robert-lippmann/ft-RPI-sa/Software/include/S32K142/S32K142_features.h

/*
 * Copyright (c) 2015 Freescale Semiconductor, Inc.
 * Copyright 2016-2023 NXP
 *
 * NXP Confidential and Proprietary. This software is owned or controlled by NXP
 * and may only be used strictly in accordance with the applicable license terms.
 * By expressly accepting such terms or by downloading, installing, activating
 * and/or otherwise using the software, you are agreeing that you have read, and
 * that you agree to comply with and are bound by, such license terms. If you do
 * not agree to be bound by the applicable license terms, then you may not retain,
 * install, activate or otherwise use the software.
 */

/*!
 * @file S32K142_features.h
 * @brief Chip specific module features
 *
 * @page misra_violations MISRA-C:2012 violations
 *
 * @section [global]
 * Violates MISRA 2012 Advisory Rule 2.3, Global typedef not referenced.
 * Type used only in some modules of the SDK.
 *
 * @section [global]
 * Violates MISRA 2012 Advisory Rule 2.4, tag unused outside of typedefs
 * Tag defined specifically for typedef
 *
 * @section [global]
 * Violates MISRA 2012 Advisory Rule 2.5, Global macro not referenced.
 * The macros defined are used to define features for each driver, so this might be reported
 * when the analysis is made only on one driver.
 *
 * @section [global]
 * Violates MISRA 2012 Advisory Directive 4.9, Function-like macro
 * These are very simple macros used for abstracting hw implementation.
 * They help make the code easy to understand.
 *
 * @section [global]
 * Violates MISRA 2012 Required Rule 5.1, identifier clash
 * The supported compilers use more than 31 significant characters for identifiers.
 *
 * @section [global]
 * Violates MISRA 2012 Required Rule 5.2, identifier clash
 * The supported compilers use more than 31 significant characters for identifiers.
 *
 * @section [global]
 * Violates MISRA 2012 Required Rule 5.4, identifier clash
 * The supported compilers use more than 31 significant characters for identifiers.
 *
 * @section [global]
 * Violates MISRA 2012 Required Rule 5.5, identifier clash
 * The supported compilers use more than 31 significant characters for identifiers.
 *
 */

#if !defined(S32K142_FEATURES_H)
#define S32K142_FEATURES_H

/* ERRATA sections*/

/* @brief ARM Errata 838869: Store immediate overlapping exception return operation might vector to
 * incorrect interrupt. */
#define ERRATA_E9005

/* @brief ARM Errata 709718: VDIV or VSQRT instructions might not complete correctly when very
 * short ISRs are used. */
#define ERRATA_E6940

/* @brief E10792: LPI2C: Slave Transmit Data Flag may incorrectly read as one when TXCFG is zero.
 * Interrupts for transfer data should be enabled after the address valid event is detected and
 * disabled at the end of the transfer. */
#define ERRATA_E10792

/* @brief Errata workaround: System clock status register may be a erroneous status during the system clock switch.
 * Read system clock source twice. */
#define ERRATA_E10777

/* @brief E10856: FTM: Safe state is not removed from channel outputs after fault condition
 * ends if SWOCTRL is being used to control the pin */
#define ERRATA_E10856

/* @brief Number of cores. */
#define NUMBER_OF_CORES (1u)

/* @brief Number of alternative clocks available */
#define NUMBER_OF_ALT_CLOCKS  ADC_CLK_ALT_1

/* PORT module features */
/*! @brief PORT Used for setting Pins */
#define FEATURE_PINS_DRIVER_USING_PORT (1)
/* @brief Has control lock (register bit PCR[LK]). */
#define FEATURE_PORT_HAS_PIN_CONTROL_LOCK (1)
/* @brief Has open drain control (register bit PCR[ODE]). */
#define FEATURE_PINS_HAS_OPEN_DRAIN (0)
/* @brief Has digital filter (registers DFER, DFCR and DFWR). */
#define FEATURE_PORT_HAS_DIGITAL_FILTER (1)
/* @brief Has trigger output to trigger other peripherals (register bit field PCR[IRQC] values). */
#define FEATURE_PORT_HAS_TRIGGER_OUT (0)
/* @brief Has setting flag only (register bit field PCR[IRQC] values). */
#define FEATURE_PORT_HAS_FLAG_SET_ONLY (0)
/* @brief Has over-current feature (register bit field PCR[OCIE] values). */
#define FEATURE_PINS_HAS_OVER_CURRENT (0)
/* @brief Has pull resistor selection available. */
#define FEATURE_PINS_HAS_PULL_SELECTION (1)
/* @brief Has slew rate control (register bit PCR[SRE]). */
#define FEATURE_PINS_HAS_SLEW_RATE (0)
/* @brief Has passive filter (register bit field PCR[PFE]). */
#define FEATURE_PORT_HAS_PASSIVE_FILTER (1)
/* @brief Has drive strength (register bit PCR[DSE]). */
#define FEATURE_PINS_HAS_DRIVE_STRENGTH (1)
/* @brief Has drive strength control bits*/
#define FEATURE_PINS_HAS_DRIVE_STRENGTH_CONTROL (0)
/* @brief Has port input disable control bits*/
#define FEATURE_PORT_HAS_INPUT_DISABLE (1)
/* @brief SIM_CHIPCTL_ADC_INTERLEAVE_EN bit is available */
#define FEATURE_PINS_HAS_ADC_INTERLEAVE_EN (1)

/* CMP module features */

/* @brief Comparator hard block offset control */
#define FEATURE_CMP_HAS_HARD_BLOCK_OFFSET   (1)
/* @brief Comparator fix DAC input to mux side */
#define FEATURE_CMP_DAC_FIX_SELECTION       (0)
/* @brief Comparator initialization delay */
#define FEATURE_CMP_HAS_INIT_DELAY          (1)

#define C0_RESET_VALUE (CMP_C0_DMAEN(0U) | CMP_C0_IER(0U) | CMP_C0_IEF(0U) | CMP_C0_CFR(1U) |                     \
                        CMP_C0_CFF(1U) | CMP_C0_FPR(0U) | CMP_C0_SE(0U) | CMP_C0_WE(0U) |                         \
                        CMP_C0_PMODE(0U) | CMP_C0_INVT(0U) | CMP_C0_COS(0U) | CMP_C0_OPE(0U) |                    \
                        CMP_C0_EN(0U) | CMP_C0_FILTER_CNT(0U) | CMP_C0_OFFSET(0U) | CMP_C0_HYSTCTR(0U))

#define C1_RESET_VALUE (CMP_C1_INPSEL(0U) | CMP_C1_INNSEL(0U) | CMP_C1_CHN7(0U) | CMP_C1_CHN6(0U) |               \
                        CMP_C1_CHN5(0U) | CMP_C1_CHN4(0U) | CMP_C1_CHN3(0U) | CMP_C1_CHN2(0U) |                   \
                        CMP_C1_CHN1(0U) | CMP_C1_CHN0(0U) | CMP_C1_DACEN(0U) | CMP_C1_VRSEL(0U) |                 \
                        CMP_C1_PSEL(0U) | CMP_C1_MSEL(0U) |  CMP_C1_VOSEL(0U))

#define C2_RESET_VALUE (CMP_C2_RRE(0U) | CMP_C2_RRIE(0U) | CMP_C2_FXMP(0U) | CMP_C2_FXMXCH(0U) | CMP_C2_CH7F(1U) |    \
                        CMP_C2_CH6F(1U) | CMP_C2_CH5F(1U) | CMP_C2_CH4F(1U) | CMP_C2_CH3F(1U) | CMP_C2_CH2F(1U) |     \
                        CMP_C2_CH1F(1U) | CMP_C2_CH0F(1U) | CMP_C2_NSAM(0U) | CMP_C2_NSAM(0U) | CMP_C2_INITMOD(0U) |  \
                        CMP_C2_ACOn(0U))

#define CMP_DAC_SOURCE          0U
#define CMP_MUX_SOURCE          1U
#define CMP_DAC_RESOLUTION      255U

/* SOC module features */

/* @brief PORT availability on the SoC. */
#define FEATURE_SOC_PORT_COUNT (5)

#define FEATURE_SOC_SCG_COUNT (1)

/* @brief Slow IRC high range clock frequency. */
#define FEATURE_SCG_SIRC_HIGH_RANGE_FREQ (8000000U)

/* @brief Fast IRC trimmed clock frequency(48MHz). */
#define FEATURE_SCG_FIRC_FREQ0  (48000000U)

/* FLASH module features */

/* @brief Is of type FTFA. */
#define FEATURE_FLS_IS_FTFA (0u)
/* @brief Is of type FTFC. */
#define FEATURE_FLS_IS_FTFC (1u)
/* @brief Is of type FTFE. */
#define FEATURE_FLS_IS_FTFE (0u)
/* @brief Is of type FTFL. */
#define FEATURE_FLS_IS_FTFL (0u)
/* @brief Is of type FTFM. */
#define FEATURE_FLS_IS_FTFM (0u)
/* @brief Has flags indicating the status of the FlexRAM (register bits FCNFG[EEERDY], FCNFG[RAMRDY] and FCNFG[PFLSH]). */
#define FEATURE_FLS_HAS_FLEX_RAM_FLAGS (1u)
/* @brief Has program flash swapping status flag (register bit FCNFG[SWAP]). */
#define FEATURE_FLS_HAS_PF_SWAPPING_STATUS_FLAG (0u)
/* @brief Has EEPROM region protection (register FEPROT). */
#define FEATURE_FLS_HAS_EEROM_REGION_PROTECTION (1u)
/* @brief Has data flash region protection (register FDPROT). */
#define FEATURE_FLS_HAS_DATA_FLS_REGION_PROTECTION (1u)
/* @brief P-Flash block count. */
#define FEATURE_FLS_PF_BLOCK_COUNT (1u)
/* @brief P-Flash block size. */
#define FEATURE_FLS_PF_BLOCK_SIZE (0x40000u)
/* @brief P-Flash sector size. */
#define FEATURE_FLS_PF_BLOCK_SECTOR_SIZE (2048u)
/* @brief P-Flash write unit size. */
#define FEATURE_FLS_PF_BLOCK_WRITE_UNIT_SIZE (8u)
/* @brief P-Flash block swap feature. */
#define FEATURE_FLS_HAS_PF_BLOCK_SWAP (0u)
/* @brief Has FlexNVM memory. */
#define FEATURE_FLS_HAS_FLEX_NVM (1u)
/* @brief FlexNVM block count. */
#define FEATURE_FLS_DF_BLOCK_COUNT (1u)
/* @brief FlexNVM block size. */
#define FEATURE_FLS_DF_BLOCK_SIZE (65536u)
/* @brief FlexNVM sector size. */
#define FEATURE_FLS_DF_BLOCK_SECTOR_SIZE (2048u)
/* @brief FlexNVM write unit size. */
#define FEATURE_FLS_DF_BLOCK_WRITE_UNIT_SIZE (8u)
/* @brief FlexNVM start address. (Valid only if FlexNVM is available.) */
#define FEATURE_FLS_DF_START_ADDRESS (0x10000000u)
/* @brief Has FlexRAM memory. */
#define FEATURE_FLS_HAS_FLEX_RAM (1u)
/* @brief FlexRAM size. */
#define FEATURE_FLS_FLEX_RAM_SIZE (4096u)
/* @brief FlexRAM start address. (Valid only if FlexRAM is available.) */
#define FEATURE_FLS_FLEX_RAM_START_ADDRESS (0x14000000u)
/* @brief Has 0x00 Read 1s Block command. */
#define FEATURE_FLS_HAS_READ_1S_BLOCK_CMD (1u)
/* @brief Has 0x01 Read 1s Section command. */
#define FEATURE_FLS_HAS_READ_1S_SECTION_CMD (1u)
/* @brief Has 0x02 Program Check command. */
#define FEATURE_FLS_HAS_PROGRAM_CHECK_CMD (1u)
/* @brief Has 0x03 Read Resource command. */
#define FEATURE_FLS_HAS_READ_RESOURCE_CMD (0u)
/* @brief Has 0x06 Program Longword command. */
#define FEATURE_FLS_HAS_PROGRAM_LONGWORD_CMD (0u)
/* @brief Has 0x07 Program Phrase command. */
#define FEATURE_FLS_HAS_PROGRAM_PHRASE_CMD (1u)
/* @brief Has 0x08 Erase Flash Block command. */
#define FEATURE_FLS_HAS_ERASE_BLOCK_CMD (1u)
/* @brief Has 0x09 Erase Flash Sector command. */
#define FEATURE_FLS_HAS_ERASE_SECTOR_CMD (1u)
/* @brief Has 0x0B Program Section command. */
#define FEATURE_FLS_HAS_PROGRAM_SECTION_CMD (1u)
/* @brief Has 0x40 Read 1s All Blocks command. */
#define FEATURE_FLS_HAS_READ_1S_ALL_BLOCKS_CMD (1u)
/* @brief Has 0x41 Read Once command. */
#define FEATURE_FLS_HAS_READ_ONCE_CMD (1u)
/* @brief Has 0x43 Program Once command. */
#define FEATURE_FLS_HAS_PROGRAM_ONCE_CMD (1u)
/* @brief Has 0x44 Erase All Blocks command. */
#define FEATURE_FLS_HAS_ERASE_ALL_CMD (1u)
/* @brief Has 0x45 Verify Backdoor Access Key command. */
#define FEATURE_FLS_HAS_VERIFY_BACKDOOR_ACCESS_KEY_CMD (1u)
/* @brief Has 0x46 Swap Control command. */
#define FEATURE_FLS_HAS_SWAP_CONTROL_CMD (0u)
/* @brief Has 0x49 Erase All Blocks unsecure command. */
#define FEATURE_FLS_HAS_ERASE_ALL_BLOCKS_UNSECURE_CMD (1u)
/* @brief Has 0x80 Program Partition command. */
#define FEATURE_FLS_HAS_PROGRAM_PARTITION_CMD (1u)
/* @brief Has 0x81 Set FlexRAM Function command. */
#define FEATURE_FLS_HAS_SET_FLEXRAM_FUNCTION_CMD (1u)
/* @brief P-Flash Erase/Read 1st all block command address alignment. */
#define FEATURE_FLS_PF_BLOCK_CMD_ADDRESS_ALIGMENT (8u)
/* @brief P-Flash Erase sector command address alignment. */
#define FEATURE_FLS_PF_SECTOR_CMD_ADDRESS_ALIGMENT (8u)
/* @brief P-Flash Program/Verify section command address alignment. */
#define FEATURE_FLS_PF_SECTION_CMD_ADDRESS_ALIGMENT (8u)
/* @brief P-Flash Read resource command address alignment. */
#define FEATURE_FLS_PF_RESOURCE_CMD_ADDRESS_ALIGMENT (8u)
/* @brief P-Flash Program check command address alignment. */
#define FEATURE_FLS_PF_CHECK_CMD_ADDRESS_ALIGMENT (4u)
/* @brief P-Flash Program check command address alignment. */
#define FEATURE_FLS_PF_SWAP_CONTROL_CMD_ADDRESS_ALIGMENT (0u)
/* @brief FlexNVM Erase/Read 1st all block command address alignment. */
#define FEATURE_FLS_DF_BLOCK_CMD_ADDRESS_ALIGMENT (8u)
/* @brief FlexNVM Erase sector command address alignment. */
#define FEATURE_FLS_DF_SECTOR_CMD_ADDRESS_ALIGMENT (8u)
/* @brief FlexNVM Program/Verify section command address alignment. */
#define FEATURE_FLS_DF_SECTION_CMD_ADDRESS_ALIGMENT (8u)
/* @brief FlexNVM Read resource command address alignment. */
#define FEATURE_FLS_DF_RESOURCE_CMD_ADDRESS_ALIGMENT (8u)
/* @brief FlexNVM Program check command address alignment. */
#define FEATURE_FLS_DF_CHECK_CMD_ADDRESS_ALIGMENT (4u)
/* @brief FlexNVM partition code 0000 mapping to data flash size in bytes (0xFFFFFFFF = reserved). */
#define FEATURE_FLS_DF_SIZE_0000 (0x00010000u)
/* @brief FlexNVM partition code 0001 mapping to data flash size in bytes (0xFFFFFFFF = reserved). */
#define FEATURE_FLS_DF_SIZE_0001 (0xFFFFFFFFu)
/* @brief FlexNVM partition code 0010 mapping to data flash size in bytes (0xFFFFFFFF = reserved). */
#define FEATURE_FLS_DF_SIZE_0010 (0xFFFFFFFFu)
/* @brief FlexNVM partition code 0011 mapping to data flash size in bytes (0xFFFFFFFF = reserved). */
#define FEATURE_FLS_DF_SIZE_0011 (0x00008000u)
/* @brief FlexNVM partition code 0100 mapping to data flash size in bytes (0xFFFFFFFF = reserved). */
#define FEATURE_FLS_DF_SIZE_0100 (0x00000000u)
/* @brief FlexNVM partition code 0101 mapping to data flash size in bytes (0xFFFFFFFF = reserved). */
#define FEATURE_FLS_DF_SIZE_0101 (0xFFFFFFFFu)
/* @brief FlexNVM partition code 0110 mapping to data flash size in bytes (0xFFFFFFFF = reserved). */
#define FEATURE_FLS_DF_SIZE_0110 (0xFFFFFFFFu)
/* @brief FlexNVM partition code 0111 mapping to data flash size in bytes (0xFFFFFFFF = reserved). */
#define FEATURE_FLS_DF_SIZE_0111 (0xFFFFFFFFu)
/* @brief FlexNVM partition code 1000 mapping to data flash size in bytes (0xFFFFFFFF = reserved). */
#define FEATURE_FLS_DF_SIZE_1000 (0x00000000u)
/* @brief FlexNVM partition code 1001 mapping to data flash size in bytes (0xFFFFFFFF = reserved). */
#define FEATURE_FLS_DF_SIZE_1001 (0xFFFFFFFFu)
/* @brief FlexNVM partition code 1010 mapping to data flash size in bytes (0xFFFFFFFF = reserved). */
#define FEATURE_FLS_DF_SIZE_1010 (0x00004000u)
/* @brief FlexNVM partition code 1011 mapping to data flash size in bytes (0xFFFFFFFF = reserved). */
#define FEATURE_FLS_DF_SIZE_1011 (0x00008000u)
/* @brief FlexNVM partition code 1100 mapping to data flash size in bytes (0xFFFFFFFF = reserved). */
#define FEATURE_FLS_DF_SIZE_1100 (0x00010000u)
/* @brief FlexNVM partition code 1101 mapping to data flash size in bytes (0xFFFFFFFF = reserved). */
#define FEATURE_FLS_DF_SIZE_1101 (0xFFFFFFFFu)
/* @brief FlexNVM partition code 1110 mapping to data flash size in bytes (0xFFFFFFFF = reserved). */
#define FEATURE_FLS_DF_SIZE_1110 (0xFFFFFFFFu)
/* @brief FlexNVM partition code 1111 mapping to data flash size in bytes (0xFFFFFFFF = reserved). */
#define FEATURE_FLS_DF_SIZE_1111 (0x00010000u)
/* @brief Emulated EEPROM size code 0000 mapping to emulated EEPROM size in bytes (0xFFFF = reserved). */
#define FEATURE_FLS_EE_SIZE_0000 (0xFFFFu)
/* @brief Emulated EEPROM size code 0001 mapping to emulated EEPROM size in bytes (0xFFFF = reserved). */
#define FEATURE_FLS_EE_SIZE_0001 (0xFFFFu)
/* @brief Emulated EEPROM size code 0010 mapping to emulated EEPROM size in bytes (0xFFFF = reserved). */
#define FEATURE_FLS_EE_SIZE_0010 (0x1000u)
/* @brief Emulated EEPROM size code 0011 mapping to emulated EEPROM size in bytes (0xFFFF = reserved). */
#define FEATURE_FLS_EE_SIZE_0011 (0xFFFFu)
/* @brief Emulated EEPROM size code 0100 mapping to emulated EEPROM size in bytes (0xFFFF = reserved). */
#define FEATURE_FLS_EE_SIZE_0100 (0xFFFFu)
/* @brief Emulated EEPROM size code 0101 mapping to emulated EEPROM size in bytes (0xFFFF = reserved). */
#define FEATURE_FLS_EE_SIZE_0101 (0xFFFFu)
/* @brief Emulated EEPROM size code 0110 mapping to emulated EEPROM size in bytes (0xFFFF = reserved). */
#define FEATURE_FLS_EE_SIZE_0110 (0xFFFFu)
/* @brief Emulated EEPROM size code 0111 mapping to emulated EEPROM size in bytes (0xFFFF = reserved). */
#define FEATURE_FLS_EE_SIZE_0111 (0xFFFFu)
/* @brief Emulated EEPROM size code 1000 mapping to emulated EEPROM size in bytes (0xFFFF = reserved). */
#define FEATURE_FLS_EE_SIZE_1000 (0xFFFFu)
/* @brief Emulated EEPROM size code 1001 mapping to emulated EEPROM size in bytes (0xFFFF = reserved). */
#define FEATURE_FLS_EE_SIZE_1001 (0xFFFFu)
/* @brief Emulated EEPROM size code 1010 mapping to emulated EEPROM size in bytes (0xFFFF = reserved). */
#define FEATURE_FLS_EE_SIZE_1010 (0xFFFFu)
/* @brief Emulated EEPROM size code 1011 mapping to emulated EEPROM size in bytes (0xFFFF = reserved). */
#define FEATURE_FLS_EE_SIZE_1011 (0xFFFFu)
/* @brief Emulated EEPROM size code 1100 mapping to emulated EEPROM size in bytes (0xFFFF = reserved). */
#define FEATURE_FLS_EE_SIZE_1100 (0xFFFFu)
/* @brief Emulated EEPROM size code 1101 mapping to emulated EEPROM size in bytes (0xFFFF = reserved). */
#define FEATURE_FLS_EE_SIZE_1101 (0xFFFFu)
/* @brief Emulated EEPROM size code 1110 mapping to emulated EEPROM size in bytes (0xFFFF = reserved). */
#define FEATURE_FLS_EE_SIZE_1110 (0xFFFFu)
/* @brief Emulated EEPROM size code 1111 mapping to emulated EEPROM size in bytes (0xFFFF = reserved). */
#define FEATURE_FLS_EE_SIZE_1111 (0x0000u)
/* @brief Has the detection of uncorrected ECC errors. */
#define FEATURE_FLS_HAS_DETECT_ECC_ERROR (1)
/* @brief Has the interrupt double bit fault detect. */
#define FEATURE_FLS_HAS_INTERRUPT_DOUBLE_BIT_FAULT_IRQ (1)

/* LPUART module features */

/* @brief Has extended data register ED. */
#define FEATURE_LPUART_HAS_EXTENDED_DATA_REGISTER_FLAGS (1)
/* @brief Hardware flow control (RTS, CTS) is supported. */
#define FEATURE_LPUART_HAS_MODEM_SUPPORT (1)
/* @brief Baud rate oversampling is available. */
#define FEATURE_LPUART_HAS_BAUD_RATE_OVER_SAMPLING_SUPPORT (1)
/* @brief Baud rate oversampling is available. */
#define FEATURE_LPUART_HAS_BOTH_EDGE_SAMPLING_SUPPORT (1)
/* @brief Capacity (number of entries) of the transmit/receive FIFO (or zero if no FIFO is available). */
#define FEATURE_LPUART_FIFO_SIZE (4U)
/* @brief Supports two match addresses to filter incoming frames. */
#define FEATURE_LPUART_HAS_ADDRESS_MATCHING (1)
/* @brief Has transmitter/receiver DMA enable bits. */
#define FEATURE_LPUART_HAS_DMA_ENABLE (1)
/* @brief Flag clearance mask for STAT register. */
#define FEATURE_LPUART_STAT_REG_FLAGS_MASK (0xC01FC000U)
/* @brief Flag clearance mask for FIFO register. */
#define FEATURE_LPUART_FIFO_REG_FLAGS_MASK (0x00030000U)
/* @brief Reset mask for FIFO register. */
#define FEATURE_LPUART_FIFO_RESET_MASK (0x0003C000U)
/* @brief Default oversampling ratio. */
#define FEATURE_LPUART_DEFAULT_OSR (0x0FUL)
/* @brief Default baud rate modulo divisor. */
#define FEATURE_LPUART_DEFAULT_SBR (0x04UL)
/* @brief Clock names for LPUART. */
#define LPUART_CLOCK_NAMES {LPUART0_CLK, LPUART1_CLK}

/* FlexIO module features */

/* @brief Define the maximum number of shifters for any FlexIO instance. */
#define FEATURE_FLEXIO_MAX_SHIFTER_COUNT  (4U)
/* @brief Define DMA request names for Flexio. */
#define FEATURE_FLEXIO_DMA_REQ_0    EDMA_REQ_FLEXIO_SHIFTER0
#define FEATURE_FLEXIO_DMA_REQ_1    EDMA_REQ_FLEXIO_SHIFTER1
#define FEATURE_FLEXIO_DMA_REQ_2    EDMA_REQ_FLEXIO_SHIFTER2
#define FEATURE_FLEXIO_DMA_REQ_3    EDMA_REQ_FLEXIO_SHIFTER3

/* LPI2C module features */

/* @brief DMA instance used for LPI2C module */
#define LPI2C_DMA_INSTANCE 0U

/* @brief EDMA requests for LPI2C module. */
#define LPI2C_EDMA_REQ                           {{(uint8_t)EDMA_REQ_LPI2C0_TX, (uint8_t)EDMA_REQ_LPI2C0_RX}}
/* @brief PCC clocks for LPI2C module. */
#define LPI2C_PCC_CLOCKS                         {LPI2C0_CLK}

/* @brief Disable high-speed and ultra-fast operating modes for S32K14x. */
#define LPI2C_HAS_FAST_PLUS_MODE (0U)
#define LPI2C_HAS_HIGH_SPEED_MODE (0U)
#define LPI2C_HAS_ULTRA_FAST_MODE (0U)

/* @brief VECTKEY value so that AIRCR register write is not ignored. */
#define FEATURE_SCB_VECTKEY               (0x05FAU)


/* SMC module features */

/* @brief Has stop option (register bit STOPCTRL[STOPO]). */
#define FEATURE_SMC_HAS_STOPO (1U)
/* @brief Has partial stop option (register bit STOPCTRL[PSTOPO]). */
#define FEATURE_SMC_HAS_PSTOPO (0U)
/* @brief Has WAIT and VLPW options. */
#define FEATURE_SMC_HAS_WAIT_VLPW (0U)
/* @brief Has high speed run mode (register bit PMPROT[AHSRUN]). */
#define FEATURE_SMC_HAS_HIGH_SPEED_RUN_MODE (1U)
/* @brief Value of SPLL source clock in the SCG_HCCR register */
#define FEATURE_SCG_SPLL_VALUE (6U)

/* RCM module feature */

/* @brief Has existence of CMU loss of clock as reset source */
#define FEATURE_RCM_HAS_EXISTENCE_CMU_LOSS_OF_CLOCK (0)
/* @brief Has CMU loss of clock as reset source */
#define FEATURE_RCM_HAS_CMU_LOSS_OF_CLOCK (0)
/* @brief Has sticky CMU loss of clock as reset source */
#define FEATURE_RCM_HAS_STICKY_CMU_LOSS_OF_CLOCK (0)

/* MPU module features */


/* @brief Specifies hardware revision level. */
#define FEATURE_MPU_HARDWARE_REVISION_LEVEL   (1U)
/* @brief Has process identifier support. */
#define FEATURE_MPU_HAS_PROCESS_IDENTIFIER    (1U)
/* @brief Special region descriptor. */
#define FEATURE_MPU_SPECIAL_REGION            (0U)
/* @brief The number of master has process identifier. */
#define FEATURE_MPU_NUM_MASTER_HAS_PROCESS_IDENTIFIER    (2U)
/* Reset value of all master access right in region 0 */
#define FEATURE_MPU_REGION_0_ACCESS_RIGHT_RESET_VALUE    (0x0061F7DFU)
/* @brief Specifies total number of bus masters. */
#define FEATURE_MPU_MASTER_COUNT              (3U)
/* @brief Specifies maximum number of masters which have separated
privilege rights for user and supervisor mode accesses (e.g. master0~3 in S32K14x).
*/
#define FEATURE_MPU_MAX_LOW_MASTER_NUMBER     (3U)
/* @brief Specifies maximum number of masters which have only
read and write permissions (e.g. master4~7 in S32K14x).
*/
#define FEATURE_MPU_MAX_HIGH_MASTER_NUMBER    (7U)

/* @brief Specifies number of set access control right bits for
   masters which have separated privilege rights for user and
   supervisor mode accesses (e.g. master0~3 in S32K14x).
*/
#define FEATURE_MPU_LOW_MASTER_CONTROL_WIDTH  (6U)
/* @brief Specifies number of set access control right bits for
   masters which have only read and write permissions(e.g. master4~7 in S32K14x).
*/
#define FEATURE_MPU_HIGH_MASTER_CONTROL_WIDTH (2U)

/* @brief The MPU Logical Bus Master Number for core bus master. */
#define FEATURE_MPU_MASTER_CORE               (0U)
/* @brief The MPU Logical Bus Master Number for Debugger master. */
#define FEATURE_MPU_MASTER_DEBUGGER           (1U)
/* @brief The MPU Logical Bus Master Number for DMA master. */
#define FEATURE_MPU_MASTER_DMA                (2U)
/* @brief Specifies master number. */
#define FEATURE_MPU_MASTER                        \
{                                                 \
    FEATURE_MPU_MASTER_CORE,     /*!< CORE */     \
    FEATURE_MPU_MASTER_DEBUGGER, /*!< DEBUGGER */ \
    FEATURE_MPU_MASTER_DMA,      /*!< DMA */      \
}

/* @brief Specifies total number of slave ports. */
#define FEATURE_MPU_SLAVE_COUNT               (4U)
/* @brief The MPU Slave Port Assignment for Flash Controller and boot ROM. */
#define FEATURE_MPU_SLAVE_FLASH_BOOTROM       (0U)
/* @brief The MPU Slave Port Assignment for SRAM back door. */
#define FEATURE_MPU_SLAVE_SRAM_BACKDOOR       (1U)
/* @brief The MPU Slave Port Assignment for SRAM_L front door. */
#define FEATURE_MPU_SLAVE_SRAM_L_FRONTDOOR    (2U)
/* @brief The MPU Slave Port Assignment for SRAM_U front door. */
#define FEATURE_MPU_SLAVE_SRAM_U_FRONTDOOR    (3U)
/* @brief The MPU Slave Port mask. */
#define FEATURE_MPU_SLAVE_MASK                (0xF0000000U)
#define FEATURE_MPU_SLAVE_SHIFT               (28u)
#define FEATURE_MPU_SLAVE_WIDTH               (4u)
#define FEATURE_MPU_SLAVE(x)                  (((uint32_t)(((uint32_t)(x))<<FEATURE_MPU_SLAVE_SHIFT))&FEATURE_MPU_SLAVE_MASK)


/* WDOG module features */

/* @brief The 32-bit value used for unlocking the WDOG. */
#define FEATURE_WDOG_UNLOCK_VALUE                       (0xD928C520U)
/* @brief The 32-bit value used for resetting the WDOG counter. */
#define FEATURE_WDOG_TRIGGER_VALUE                      (0xB480A602U)
/* @brief The reset value of the timeout register. */
#define FEATURE_WDOG_TO_RESET_VALUE                     (0x400U)
/* @brief The value minimum of the timeout register. */
#define FEATURE_WDOG_MINIMUM_TIMEOUT_VALUE              (0x0U)
/* @brief The reset value of the window register. */
#define FEATURE_WDOG_WIN_RESET_VALUE                    (0x0U)
/* @brief The mask of the reserved bit in the CS register. */
#define FEATURE_WDOG_CS_RESERVED_MASK                   (0x2000U)
/* @brief The value used to set WDOG source clock from LPO. */
#define FEATURE_WDOG_CLK_FROM_LPO                       (0x1UL)
/* @brief The first 16-bit value used for unlocking the WDOG. */
#define FEATURE_WDOG_UNLOCK16_FIRST_VALUE               (0xC520U)
/* @brief The second 16-bit value used for unlocking the WDOG. */
#define FEATURE_WDOG_UNLOCK16_SECOND_VALUE              (0xD928U)
/* @brief The first 16-bit value used for resetting the WDOG counter. */
#define FEATURE_WDOG_TRIGGER16_FIRST_VALUE              (0xA602U)
/* @brief The second 16-bit value used for resetting the WDOG counter. */
#define FEATURE_WDOG_TRIGGER16_SECOND_VALUE             (0xB480U)
/* @brief Default reset value of the CS register. */
#define FEATURE_WDOG_CS_RESET_VALUE                     (0x2520U)

/* FTM module features */

/* @brief Number of PWM channels */
#define FEATURE_FTM_CHANNEL_COUNT               (8U)
/* @brief Number of fault channels */
#define FTM_FEATURE_FAULT_CHANNELS              (4U)
/* @brief Width of control channel */
#define FTM_FEATURE_COMBINE_CHAN_CTRL_WIDTH     (8U)
/* @brief Output channel offset */
#define FTM_FEATURE_OUTPUT_CHANNEL_OFFSET       (16U)
/* @brief Max counter value */
#define FTM_FEATURE_CNT_MAX_VALUE_U32           (0x0000FFFFU)
/* @brief Input capture for single shot */
#define FTM_FEATURE_INPUT_CAPTURE_SINGLE_SHOT   (2U)
/* @brief Dithering has supported on the generated PWM signals */
#define FEATURE_FTM_HAS_SUPPORTED_DITHERING     (1U)
/*! @brief Number of interrupt vector for channels of the FTM module. */
#define FEATURE_FTM_HAS_NUM_IRQS_CHANS          (4U)

/* CRC module features */

/* @brief CRC module use for S32K. */
#define FEATURE_CRC_DRIVER_SOFT_POLYNOMIAL
/* @brief Default CRC bit width */
#define FEATURE_CRC_DEFAULT_WIDTH               CRC_BITS_16
/* @brief Default CRC read transpose */
#define FEATURE_CRC_DEFAULT_READ_TRANSPOSE      CRC_TRANSPOSE_NONE
/* @brief Default CRC write transpose */
#define FEATURE_CRC_DEFAULT_WRITE_TRANSPOSE     CRC_TRANSPOSE_NONE
/* @brief Default polynomial 0x1021U */
#define FEATURE_CRC_DEFAULT_POLYNOMIAL          (0x1021U)
/* @brief Default seed value is 0xFFFFU */
#define FEATURE_CRC_DEFAULT_SEED                (0xFFFFU)

/* EWM module features */

/* @brief First byte of the EWM Service key        */
#define FEATURE_EWM_KEY_FIRST_BYTE      (0xB4U)
/* @brief Second byte of the EWM Service key       */
#define FEATURE_EWM_KEY_SECOND_BYTE     (0x2CU)
/* @brief EWM Compare High register maximum value  */
#define FEATURE_EWM_CMPH_MAX_VALUE      (0xFEU)
/* @brief EWM Compare Low register minimum value  */
#define FEATURE_EWM_CMPL_MIN_VALUE      (0x00U)

/* @brief Supports high speed run mode. */
#define FEATURE_HAS_HIGH_SPEED_RUN_MODE  (1U)
/* @brief Supports SPLL clock source. */
#define FEATURE_HAS_SPLL_CLK             (1U)
/* @brief Supports LPO peripheral clock source. */
#define FEATURE_HAS_LPO_PERIPHERAL_CLOCK_SOURCE (0U)

/*! @brief Clock names. */
typedef enum {

    /* Main clocks */
    CORE_CLK                     = 0u,       /*!< Core clock                     */
    BUS_CLK                      = 1u,       /*!< Bus clock                      */
    SLOW_CLK                     = 2u,       /*!< Slow clock                     */
    CLKOUT_CLK                   = 3u,       /*!< CLKOUT clock                   */

    /* Other internal clocks used by peripherals. */
    SIRC_CLK                     = 4u,       /*!< SIRC clock                     */
    FIRC_CLK                     = 5u,       /*!< FIRC clock                     */
    SOSC_CLK                     = 6u,       /*!< SOSC clock                     */
    SPLL_CLK                     = 7u,       /*!< SPLL clock                     */
    RTC_CLKIN_CLK                = 8u,       /*!< RTC_CLKIN clock                */
    SCG_CLKOUT_CLK               = 9u,       /*!< SCG CLK_OUT clock              */

    SIRCDIV1_CLK                 = 10u,      /*!< SIRCDIV1 functional clock      */
    SIRCDIV2_CLK                 = 11u,      /*!< SIRCDIV2 functional clock      */
    FIRCDIV1_CLK                 = 12u,      /*!< FIRCDIV1 functional clock      */
    FIRCDIV2_CLK                 = 13u,      /*!< FIRCDIV2 functional clock      */
    SOSCDIV1_CLK                 = 14u,      /*!< SOSCDIV1 functional clock      */
    SOSCDIV2_CLK                 = 15u,      /*!< SOSCDIV2 functional clock      */
    SPLLDIV1_CLK                 = 16u,      /*!< SPLLDIV1 functional clock      */
    SPLLDIV2_CLK                 = 17u,      /*!< SPLLDIV2 functional clock      */

    SCG_END_OF_CLOCKS            = 18u,      /*!< End of SCG clocks              */

    /* SIM clocks */
    SIM_FTM0_CLOCKSEL            = 21u,      /*!< FTM0 External Clock Pin Select */
    SIM_FTM1_CLOCKSEL            = 22u,      /*!< FTM1 External Clock Pin Select */
    SIM_FTM2_CLOCKSEL            = 23u,      /*!< FTM2 External Clock Pin Select */
    SIM_FTM3_CLOCKSEL            = 24u,      /*!< FTM3 External Clock Pin Select */
    SIM_CLKOUTSELL               = 25u,      /*!< CLKOUT Select                  */
    SIM_RTCCLK_CLK               = 26u,      /*!< RTCCLK clock                   */
    SIM_LPO_CLK                  = 27u,      /*!< LPO clock                      */
    SIM_LPO_1K_CLK               = 28u,      /*!< LPO 1KHz clock                 */
    SIM_LPO_32K_CLK              = 29u,      /*!< LPO 32KHz clock                */
    SIM_LPO_128K_CLK             = 30u,      /*!< LPO 128KHz clock               */
    SIM_EIM_CLK                  = 31u,      /*!< EIM clock source               */
    SIM_ERM_CLK                  = 32u,      /*!< ERM clock source               */
    SIM_DMA_CLK                  = 33u,      /*!< DMA clock source               */
    SIM_MPU_CLK                  = 34u,      /*!< MPU clock source               */
    SIM_MSCM_CLK                 = 35u,      /*!< MSCM clock source              */
    SIM_END_OF_CLOCKS            = 36u,      /*!< End of SIM clocks              */

    /* PCC clocks */
    CMP0_CLK                     = 41u,      /*!< CMP0 clock source              */
    CRC0_CLK                     = 42u,      /*!< CRC0 clock source              */
    DMAMUX0_CLK                  = 43u,      /*!< DMAMUX0 clock source           */
    EWM0_CLK                     = 44u,      /*!< EWM0 clock source              */
    PORTA_CLK                    = 45u,      /*!< PORTA clock source             */
    PORTB_CLK                    = 46u,      /*!< PORTB clock source             */
    PORTC_CLK                    = 47u,      /*!< PORTC clock source             */
    PORTD_CLK                    = 48u,      /*!< PORTD clock source             */
    PORTE_CLK                    = 49u,      /*!< PORTE clock source             */
    RTC0_CLK                     = 50u,      /*!< RTC0 clock source              */
    PCC_END_OF_BUS_CLOCKS        = 51u,      /*!< End of BUS clocks              */
    FlexCAN0_CLK                 = 52u,      /*!< FlexCAN0 clock source          */
    FlexCAN1_CLK                 = 53u,      /*!< FlexCAN1 clock source          */
    PDB0_CLK                     = 54u,      /*!< PDB0 clock source              */
    PDB1_CLK                     = 55u,      /*!< PDB1 clock source              */
    PCC_END_OF_SYS_CLOCKS        = 56u,      /*!< End of SYS clocks              */
    FTFC0_CLK                    = 57u,      /*!< FTFC0 clock source             */
    PCC_END_OF_SLOW_CLOCKS       = 58u,      /*!< End of SLOW clocks             */
    FTM0_CLK                     = 59u,      /*!< FTM0 clock source              */
    FTM1_CLK                     = 60u,      /*!< FTM1 clock source              */
    FTM2_CLK                     = 61u,      /*!< FTM2 clock source              */
    FTM3_CLK                     = 62u,      /*!< FTM3 clock source              */
    PCC_END_OF_ASYNCH_DIV1_CLOCKS= 63u,      /*!< End of ASYNCH DIV1 clocks      */
    ADC0_CLK                     = 64u,      /*!< ADC0 clock source              */
    ADC1_CLK                     = 65u,      /*!< ADC1 clock source              */
    FLEXIO0_CLK                  = 66u,      /*!< FLEXIO0 clock source           */
    LPI2C0_CLK                   = 67u,      /*!< LPI2C0 clock source            */
    LPIT0_CLK                    = 68u,      /*!< LPIT0 clock source             */
    LPSPI0_CLK                   = 69u,      /*!< LPSPI0 clock source            */
    LPSPI1_CLK                   = 70u,      /*!< LPSPI1 clock source            */
    LPTMR0_CLK                   = 71u,      /*!< LPTMR0 clock source            */
    LPUART0_CLK                  = 72u,      /*!< LPUART0 clock source           */
    LPUART1_CLK                  = 73u,      /*!< LPUART1 clock source           */
    PCC_END_OF_ASYNCH_DIV2_CLOCKS= 74u,      /*!< End of ASYNCH DIV2 clocks      */
    PCC_END_OF_CLOCKS            = 75u,      /*!< End of PCC clocks              */
    CLOCK_NAME_COUNT             = 76u,      /*!< The total number of entries    */
} clock_names_t;

#define PCC_INVALID_INDEX  0

  /*! @brief PCC clock name mappings
   *  Mappings between clock names and peripheral clock control indexes.
   *  If there is no peripheral clock control index for a clock name,
   *  then the corresponding value is PCC_INVALID_INDEX.
   */
#define PCC_CLOCK_NAME_MAPPINGS \
{                                                                                \
PCC_INVALID_INDEX,                  /*!< Core clock                      0  */   \
PCC_INVALID_INDEX,                  /*!< Bus clock                       1  */   \
PCC_INVALID_INDEX,                  /*!< Slow clock                      2  */   \
PCC_INVALID_INDEX,                  /*!< CLKOUT clock                    3  */   \
PCC_INVALID_INDEX,                  /*!< SIRC clock                      4  */   \
PCC_INVALID_INDEX,                  /*!< FIRC clock                      5  */   \
PCC_INVALID_INDEX,                  /*!< SOSC clock                      6  */   \
PCC_INVALID_INDEX,                  /*!< SPLL clock                      7  */   \
PCC_INVALID_INDEX,                  /*!< RTC_CLKIN clock                 8  */   \
PCC_INVALID_INDEX,                  /*!< SCG CLK_OUT clock               9  */   \
PCC_INVALID_INDEX,                  /*!< SIRCDIV1 functional clock       10 */   \
PCC_INVALID_INDEX,                  /*!< SIRCDIV2 functional clock       11 */   \
PCC_INVALID_INDEX,                  /*!< FIRCDIV1 functional clock       12 */   \
PCC_INVALID_INDEX,                  /*!< FIRCDIV2 functional clock       13 */   \
PCC_INVALID_INDEX,                  /*!< SOSCDIV1 functional clock       14 */   \
PCC_INVALID_INDEX,                  /*!< SOSCDIV2 functional clock       15 */   \
PCC_INVALID_INDEX,                  /*!< SPLLDIV1 functional clock       16 */   \
PCC_INVALID_INDEX,                  /*!< SPLLDIV2 functional clock       17 */   \
PCC_INVALID_INDEX,                  /*!< End of SCG clocks               18 */   \
PCC_INVALID_INDEX,                  /*!< No clock entry in clock_names_t 19 */   \
PCC_INVALID_INDEX,                  /*!< No clock entry in clock_names_t 20 */   \
PCC_INVALID_INDEX,                  /*!< FTM0 External Clock Pin Select  21 */   \
PCC_INVALID_INDEX,                  /*!< FTM1 External Clock Pin Select  22 */   \
PCC_INVALID_INDEX,                  /*!< FTM2 External Clock Pin Select  23 */   \
PCC_INVALID_INDEX,                  /*!< FTM3 External Clock Pin Select  24 */   \
PCC_INVALID_INDEX,                  /*!< CLKOUT Select                   25 */   \
PCC_INVALID_INDEX,                  /*!< CLK32K clock                    26 */   \
PCC_INVALID_INDEX,                  /*!< LPO clock                       27 */   \
PCC_INVALID_INDEX,                  /*!< LPO 1KHz clock                  28 */   \
PCC_INVALID_INDEX,                  /*!< LPO 32KHz clock                 29 */   \
PCC_INVALID_INDEX,                  /*!< LPO 128KHz clock                30 */   \
PCC_INVALID_INDEX,                  /*!< EIM clock source                31 */   \
PCC_INVALID_INDEX,                  /*!< ERM clock source                32 */   \
PCC_INVALID_INDEX,                  /*!< DMA clock source                33 */   \
PCC_INVALID_INDEX,                  /*!< MPU clock source                34 */   \
PCC_INVALID_INDEX,                  /*!< MSCM clock source               35 */   \
PCC_INVALID_INDEX,                  /*!< No clock entry in clock_names_t 36 */   \
PCC_INVALID_INDEX,                  /*!< No clock entry in clock_names_t 37 */   \
PCC_INVALID_INDEX,                  /*!< No clock entry in clock_names_t 38 */   \
PCC_INVALID_INDEX,                  /*!< No clock entry in clock_names_t 39 */   \
PCC_INVALID_INDEX,                  /*!< No clock entry in clock_names_t 40 */   \
PCC_CMP0_INDEX,                     /*!< CMP0 clock source               41 */   \
PCC_CRC_INDEX,                      /*!< CRC clock source                42 */   \
PCC_DMAMUX_INDEX,                   /*!< DMAMUX clock source             43 */   \
PCC_EWM_INDEX,                      /*!< EWM clock source                44 */   \
PCC_PORTA_INDEX,                    /*!< PORTA clock source              45 */   \
PCC_PORTB_INDEX,                    /*!< PORTB clock source              46 */   \
PCC_PORTC_INDEX,                    /*!< PORTC clock source              47 */   \
PCC_PORTD_INDEX,                    /*!< PORTD clock source              48 */   \
PCC_PORTE_INDEX,                    /*!< PORTE clock source              49 */   \
PCC_RTC_INDEX,                      /*!< RTC clock source                50 */   \
PCC_INVALID_INDEX,                  /*!< End of BUS clocks               51 */   \
PCC_FlexCAN0_INDEX,                 /*!< FlexCAN0 clock source           52 */   \
PCC_FlexCAN1_INDEX,                 /*!< FlexCAN1 clock source           53 */   \
PCC_PDB0_INDEX,                     /*!< PDB0 clock source               54 */   \
PCC_PDB1_INDEX,                     /*!< PDB1 clock source               55 */   \
PCC_INVALID_INDEX,                  /*!< End of SYS clocks               56 */   \
PCC_FTFC_INDEX,                     /*!< FTFC clock source               57 */   \
PCC_INVALID_INDEX,                  /*!< End of SLOW clocks              58 */   \
PCC_FTM0_INDEX,                     /*!< FTM0 clock source               59 */   \
PCC_FTM1_INDEX,                     /*!< FTM1 clock source               60 */   \
PCC_FTM2_INDEX,                     /*!< FTM2 clock source               61 */   \
PCC_FTM3_INDEX,                     /*!< FTM3 clock source               62 */   \
PCC_INVALID_INDEX,                  /*!< End of ASYNCH DIV1 clocks       63 */   \
PCC_ADC0_INDEX,                     /*!< ADC0 clock source               64 */   \
PCC_ADC1_INDEX,                     /*!< ADC1 clock source               65 */   \
PCC_FlexIO_INDEX,                   /*!< FLEXIO clock source             66 */   \
PCC_LPI2C0_INDEX,                   /*!< LPI2C0 clock source             67 */   \
PCC_LPIT_INDEX,                     /*!< LPIT clock source               68 */   \
PCC_LPSPI0_INDEX,                   /*!< LPSPI0 clock source             69 */   \
PCC_LPSPI1_INDEX,                   /*!< LPSPI1 clock source             70 */   \
PCC_LPTMR0_INDEX,                   /*!< LPTMR0 clock source             71 */   \
PCC_LPUART0_INDEX,                  /*!< LPUART0 clock source            72 */   \
PCC_LPUART1_INDEX,                  /*!< LPUART1 clock source            73 */   \
PCC_INVALID_INDEX,                  /*!< End of ASYNCH DIV2 clocks       74 */   \
PCC_INVALID_INDEX,                  /*!< End of PCC clocks               75 */   \
}

/*! @brief Peripheral instance features
 *  List of features that are supported by a peripheral instance
 */
#define NO_PERIPHERAL_FEATURE                   (0U)         /* It's not a peripheral instance, there is no peripheral feature. */
#define HAS_CLOCK_GATING_IN_SIM                 (1U << 0U)   /* Clock gating is implemented in SIM (it's not in PCC) */
#define HAS_MULTIPLIER                          (1U << 1U)   /* Multiplier is implemented in PCC */
#define HAS_DIVIDER                             (1U << 2U)   /* Divider is implemented in PCC */
#define HAS_PROTOCOL_CLOCK_FROM_ASYNC1          (1U << 3U)   /* Functional clock source is provided by the first asynchronous clock. */
#define HAS_PROTOCOL_CLOCK_FROM_ASYNC2          (1U << 4U)   /* Functional clock source is provided by the second asynchronous clock. */
#define HAS_INT_CLOCK_FROM_BUS_CLOCK            (1U << 5U)   /* Interface clock is provided by the bus clock. */
#define HAS_INT_CLOCK_FROM_SYS_CLOCK            (1U << 6U)   /* Interface clock is provided by the sys clock. */
#define HAS_INT_CLOCK_FROM_SLOW_CLOCK           (1U << 7U)   /* Interface clock is provided by the slow clock. */

/*! @brief Peripheral features.
*  List of features for each clock name. If a clock name is not
*  a peripheral, no feature is supported.
*/
#define PERIPHERAL_FEATURES \
{                                                                                                                                                \
(NO_PERIPHERAL_FEATURE),                                                                            /*!< Core clock                      0  */   \
(NO_PERIPHERAL_FEATURE),                                                                            /*!< Bus clock                       1  */   \
(NO_PERIPHERAL_FEATURE),                                                                            /*!< Slow clock                      2  */   \
(NO_PERIPHERAL_FEATURE),                                                                            /*!< CLKOUT clock                    3  */   \
(NO_PERIPHERAL_FEATURE),                                                                            /*!< SIRC clock                      4  */   \
(NO_PERIPHERAL_FEATURE),                                                                            /*!< FIRC clock                      5  */   \
(NO_PERIPHERAL_FEATURE),                                                                            /*!< SOSC clock                      6  */   \
(NO_PERIPHERAL_FEATURE),                                                                            /*!< SPLL clock                      7  */   \
(NO_PERIPHERAL_FEATURE),                                                                            /*!< RTC_CLKIN clock                 8  */   \
(NO_PERIPHERAL_FEATURE),                                                                            /*!< SCG CLK_OUT clock               9  */   \
(NO_PERIPHERAL_FEATURE),                                                                            /*!< End of SCG clocks               10 */   \
(NO_PERIPHERAL_FEATURE),                                                                            /*!< No clock entry in clock_names_t 11 */   \
(NO_PERIPHERAL_FEATURE),                                                                            /*!< No clock entry in clock_names_t 12 */   \
(NO_PERIPHERAL_FEATURE),                                                                            /*!< No clock entry in clock_names_t 13 */   \
(NO_PERIPHERAL_FEATURE),                                                                            /*!< No clock entry in clock_names_t 14 */   \
(NO_PERIPHERAL_FEATURE),                                                                            /*!< No clock entry in clock_names_t 15 */   \
(NO_PERIPHERAL_FEATURE),                                                                            /*!< No clock entry in clock_names_t 16 */   \
(NO_PERIPHERAL_FEATURE),                                                                            /*!< No clock entry in clock_names_t 17 */   \
(NO_PERIPHERAL_FEATURE),                                                                            /*!< No clock entry in clock_names_t 18 */   \
(NO_PERIPHERAL_FEATURE),                                                                            /*!< No clock entry in clock_names_t 19 */   \
(NO_PERIPHERAL_FEATURE),                                                                            /*!< No clock entry in clock_names_t 20 */   \
(NO_PERIPHERAL_FEATURE),                                                                            /*!< FTM0 External Clock Pin Select  21 */   \
(NO_PERIPHERAL_FEATURE),                                                                            /*!< FTM1 External Clock Pin Select  22 */   \
(NO_PERIPHERAL_FEATURE),                                                                            /*!< FTM2 External Clock Pin Select  23 */   \
(NO_PERIPHERAL_FEATURE),                                                                            /*!< FTM3 External Clock Pin Select  24 */   \
(NO_PERIPHERAL_FEATURE),                                                                            /*!< CLKOUT Select                   25 */   \
(NO_PERIPHERAL_FEATURE),                                                                            /*!< CLK32K clock                    26 */   \
(NO_PERIPHERAL_FEATURE),                                                                            /*!< LPO clock                       27 */   \
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
(NO_PERIPHERAL_FEATURE),                                                                            /*!< End of SYS clocks               56 */   \
(HAS_INT_CLOCK_FROM_SLOW_CLOCK),                                                                    /*!< FTFC clock source               57 */   \
(NO_PERIPHERAL_FEATURE),                                                                            /*!< End of SLOW clocks              58 */   \
(HAS_PROTOCOL_CLOCK_FROM_ASYNC1 | HAS_INT_CLOCK_FROM_SYS_CLOCK),                                    /*!< FTM0 clock source               59 */   \
(HAS_PROTOCOL_CLOCK_FROM_ASYNC1 | HAS_INT_CLOCK_FROM_SYS_CLOCK),                                    /*!< FTM1 clock source               60 */   \
(HAS_PROTOCOL_CLOCK_FROM_ASYNC1 | HAS_INT_CLOCK_FROM_SYS_CLOCK),                                    /*!< FTM2 clock source               61 */   \
(HAS_PROTOCOL_CLOCK_FROM_ASYNC1 | HAS_INT_CLOCK_FROM_SYS_CLOCK),                                    /*!< FTM3 clock source               62 */   \
(NO_PERIPHERAL_FEATURE),                                                                            /*!< End of ASYNCH DIV1 clocks       63 */   \
(HAS_PROTOCOL_CLOCK_FROM_ASYNC2 | HAS_INT_CLOCK_FROM_BUS_CLOCK),                                    /*!< ADC0 clock source               64 */   \
(HAS_PROTOCOL_CLOCK_FROM_ASYNC2 | HAS_INT_CLOCK_FROM_BUS_CLOCK),                                    /*!< ADC1 clock source               65 */   \
(HAS_PROTOCOL_CLOCK_FROM_ASYNC2 | HAS_INT_CLOCK_FROM_BUS_CLOCK),                                    /*!< FLEXIO clock source             66 */   \
(HAS_PROTOCOL_CLOCK_FROM_ASYNC2 | HAS_INT_CLOCK_FROM_BUS_CLOCK),                                    /*!< LPI2C0 clock source             67 */   \
(HAS_PROTOCOL_CLOCK_FROM_ASYNC2 | HAS_INT_CLOCK_FROM_BUS_CLOCK),                                    /*!< LPIT clock source               68 */   \
(HAS_PROTOCOL_CLOCK_FROM_ASYNC2 | HAS_INT_CLOCK_FROM_BUS_CLOCK),                                    /*!< LPSPI0 clock source             69 */   \
(HAS_PROTOCOL_CLOCK_FROM_ASYNC2 | HAS_INT_CLOCK_FROM_BUS_CLOCK),                                    /*!< LPSPI1 clock source             70 */   \
(HAS_MULTIPLIER | HAS_DIVIDER | HAS_PROTOCOL_CLOCK_FROM_ASYNC2 | HAS_INT_CLOCK_FROM_BUS_CLOCK),     /*!< LPTMR0 clock source             71 */   \
(HAS_PROTOCOL_CLOCK_FROM_ASYNC2 | HAS_INT_CLOCK_FROM_BUS_CLOCK),                                    /*!< LPUART0 clock source            72 */   \
(HAS_PROTOCOL_CLOCK_FROM_ASYNC2 | HAS_INT_CLOCK_FROM_BUS_CLOCK),                                    /*!< LPUART1 clock source            73 */   \
(NO_PERIPHERAL_FEATURE),                                                                            /*!< End of ASYNCH DIV2 clocks       74 */   \
(NO_PERIPHERAL_FEATURE),                                                                            /*!< End of PCC clocks               75 */   \
}


/* Time to wait for SIRC to stabilize (number of
 * cycles when core runs at maximum speed - 112 MHz */
#define SIRC_STABILIZATION_TIMEOUT 100U

/* Time to wait for FIRC to stabilize (number of
 * cycles when core runs at maximum speed - 112 MHz */
#define FIRC_STABILIZATION_TIMEOUT 100U

/* Time to wait for SOSC to stabilize (number of
 * cycles when core runs at maximum speed - 112 MHz */
#define SOSC_STABILIZATION_TIMEOUT 3205000U;

/* Time to wait for SPLL to stabilize (number of
 * cycles when core runs at maximum speed - 112 MHz */
#define SPLL_STABILIZATION_TIMEOUT 1000U;


/*! @brief Temporary system clock source configurations.
 *         Each line represents the SYS(CORE), BUS and SLOW(FLASH) dividers
 *         for SIRC, FIRC, SOSC and SPLL clock sources.
  *
 *          SYS_CLK  BUS_CLK  SLOW_CLK
 *  SIRC       *        *         *
 *  FIRC       *        *         *
 *  SOSC       *        *         *
 *  SPLL       *        *         *
 */
#define TMP_SIRC_CLK   0U
#define TMP_FIRC_CLK   1U
#define TMP_SOSC_CLK   2U
#define TMP_SPLL_CLK   3U

#define TMP_SYS_DIV    0U
#define TMP_BUS_DIV    1U
#define TMP_SLOW_DIV   2U

#define TMP_SYS_CLK_NO 4U
#define TMP_SYS_DIV_NO 3U

#define TMP_SYSTEM_CLOCK_CONFIGS                                                                                \
{  /*       SYS_CLK                    BUS_CLK                  SLOW_CLK      */                                \
{  SCG_SYSTEM_CLOCK_DIV_BY_1, SCG_SYSTEM_CLOCK_DIV_BY_1, SCG_SYSTEM_CLOCK_DIV_BY_2},  /*!< Dividers for SIRC */ \
{  SCG_SYSTEM_CLOCK_DIV_BY_1, SCG_SYSTEM_CLOCK_DIV_BY_2, SCG_SYSTEM_CLOCK_DIV_BY_4},  /*!< Dividers for FIRC */ \
{  SCG_SYSTEM_CLOCK_DIV_BY_1, SCG_SYSTEM_CLOCK_DIV_BY_2, SCG_SYSTEM_CLOCK_DIV_BY_2},  /*!< Dividers for SOSC */ \
{  SCG_SYSTEM_CLOCK_DIV_BY_3, SCG_SYSTEM_CLOCK_DIV_BY_2, SCG_SYSTEM_CLOCK_DIV_BY_2},  /*!< Dividers for SPLL */ \
}
/* @brief template system clock configuration in VLPR mode*/
#define FEATURE_VLPR_SYS_CLK SCG_SYSTEM_CLOCK_DIV_BY_2
#define FEATURE_VLPR_BUS_CLK SCG_SYSTEM_CLOCK_DIV_BY_1
#define FEATURE_VLPR_SLOW_CLK SCG_SYSTEM_CLOCK_DIV_BY_4

/* Do not use the old names of the renamed symbols */
/* #define DO_NOT_USE_DEPRECATED_SYMBOLS */

/*! START !DO_NOT_USE_DEPRECATED_SYMBOLS
 *  These symbols have been renamed.
 *  The old names (deprecated symbols)
 *  are defined for backward compatibility.
 */
#if !defined(DO_NOT_USE_DEPRECATED_SYMBOLS)
#define    CORE_CLOCK               CORE_CLK
#define    BUS_CLOCK                BUS_CLK
#define    SLOW_CLOCK               SLOW_CLK
#define    CLKOUT_CLOCK             CLKOUT_CLK
#define    SIRC_CLOCK               SIRC_CLK
#define    FIRC_CLOCK               FIRC_CLK
#define    SOSC_CLOCK               SOSC_CLK
#define    SPLL_CLOCK               SPLL_CLK
#define    RTC_CLKIN_CLOCK          RTC_CLKIN_CLK
#define    SCG_CLKOUT_CLOCK         SCG_CLKOUT_CLK
#define    SIM_RTCCLK_CLOCK         SIM_RTCCLK_CLK
#define    SIM_LPO_CLOCK            SIM_LPO_CLK
#define    SIM_LPO_1K_CLOCK         SIM_LPO_1K_CLK
#define    SIM_LPO_32K_CLOCK        SIM_LPO_32K_CLK
#define    SIM_LPO_128K_CLOCK       SIM_LPO_128K_CLK
#define    SIM_EIM_CLOCK            SIM_EIM_CLK
#define    SIM_ERM_CLOCK            SIM_ERM_CLK
#define    SIM_DMA_CLOCK            SIM_DMA_CLK
#define    SIM_MPU_CLOCK            SIM_MPU_CLK
#define    SIM_MSCM_CLOCK           SIM_MSCM_CLK
#define    PCC_DMAMUX0_CLOCK        DMAMUX0_CLK
#define    PCC_CRC0_CLOCK           CRC0_CLK
#define    PCC_RTC0_CLOCK           RTC0_CLK
#define    PCC_PORTA_CLOCK          PORTA_CLK
#define    PCC_PORTB_CLOCK          PORTB_CLK
#define    PCC_PORTC_CLOCK          PORTC_CLK
#define    PCC_PORTD_CLOCK          PORTD_CLK
#define    PCC_PORTE_CLOCK          PORTE_CLK
#define    PCC_EWM0_CLOCK           EWM0_CLK
#define    PCC_CMP0_CLOCK           CMP0_CLK
#define    PCC_FlexCAN0_CLOCK       FlexCAN0_CLK
#define    PCC_FlexCAN1_CLOCK       FlexCAN1_CLK
#define    PCC_FlexCAN2_CLOCK       FlexCAN2_CLK
#define    PCC_PDB1_CLOCK           PDB1_CLK
#define    PCC_PDB0_CLOCK           PDB0_CLK
#define    PCC_FTFC0_CLOCK          FTFC0_CLK
#define    PCC_FTM0_CLOCK           FTM0_CLK
#define    PCC_FTM1_CLOCK           FTM1_CLK
#define    PCC_FTM2_CLOCK           FTM2_CLK
#define    PCC_FTM3_CLOCK           FTM3_CLK
#define    PCC_ADC1_CLOCK           ADC1_CLK
#define    PCC_LPSPI0_CLOCK         LPSPI0_CLK
#define    PCC_LPSPI1_CLOCK         LPSPI1_CLK
#define    PCC_LPSPI2_CLOCK         LPSPI2_CLK
#define    PCC_LPIT0_CLOCK          LPIT0_CLK
#define    PCC_ADC0_CLOCK           ADC0_CLK
#define    PCC_LPTMR0_CLOCK         LPTMR0_CLK
#define    PCC_FLEXIO0_CLOCK        FLEXIO0_CLK
#define    PCC_LPI2C0_CLOCK         LPI2C0_CLK
#define    PCC_LPUART0_CLOCK        LPUART0_CLK
#define    PCC_LPUART1_CLOCK        LPUART1_CLK
#define    PCC_LPUART2_CLOCK        LPUART2_CLK
#endif /* !DO_NOT_USE_DEPRECATED_SYMBOLS */


/* Interrupt module features */

/* @brief Lowest interrupt request number. */
#define FEATURE_INTERRUPT_IRQ_MIN         (NonMaskableInt_IRQn)
/* @brief Highest interrupt request number. */
#define FEATURE_INTERRUPT_IRQ_MAX         (FTM3_Ovf_Reload_IRQn)
/**< Number of priority bits implemented in the NVIC */
#define FEATURE_NVIC_PRIO_BITS            (4U)
/* @brief Has software interrupt. */
#define FEATURE_INTERRUPT_HAS_SOFTWARE_IRQ  (0u)
/* @brief Has pending interrupt state. */
#define FEATURE_INTERRUPT_HAS_PENDING_STATE (1u)
/* @brief Has active interrupt state. */
#define FEATURE_INTERRUPT_HAS_ACTIVE_STATE  (1u)
/* @brief Multicore support for interrupts */
#define FEATURE_INTERRUPT_MULTICORE_SUPPORT  (0u)
/* @brief Registers in which the start of interrupt vector table needs to be configured */
#define FEATURE_INTERRUPT_INT_VECTORS {&S32_SCB->VTOR}

/* CSEc module features */

/*! @brief CSE_PRAM offset of the page length parameter used by the following
commands: CMD_ENC_ECB, CMD_ENC_CBC, CMD_DEC_ECB, CMD_DEC_CBC, CMD_MP_COMPRESS */
#define FEATURE_CSEC_PAGE_LENGTH_OFFSET                   (0xEU)
/*! @brief CSE_PRAM offset of the message length parameter used by the following
commands: CMD_GENERATE_MAC, CMD_VERIFY_MAC (both copy and pointer methods) */
#define FEATURE_CSEC_MESSAGE_LENGTH_OFFSET                (0xCU)
/*! @brief CSE_PRAM offset of the MAC length parameter used by the following
commands: CMD_VERIFY_MAC (both copy and pointer methods) */
#define FEATURE_CSEC_MAC_LENGTH_OFFSET                    (0x8U)
/*! @brief CSE_PRAM offset of the boot size parameter used by the following
commands: CMD_BOOT_DEFINE */
#define FEATURE_CSEC_BOOT_SIZE_OFFSET                     (0x1CU)
/*! @brief CSE_PRAM offset of the boot flavor parameter used by the following
commands: CMD_BOOT_DEFINE */
#define FEATURE_CSEC_BOOT_FLAVOR_OFFSET                   (0x1BU)
/*! @brief CSE_PRAM offset of the Flash start address parameter used by the
following commands: CMD_GENERATE_MAC, CMD_VERIFY_MAC (pointer method) */
#define FEATURE_CSEC_FLASH_START_ADDRESS_OFFSET           (0x10U)
/*! @brief CSE_PRAM offset of the verification status parameter used by the
following commands: CMD_VERIFY_MAC (both copy and pointer methods) */
#define FEATURE_CSEC_VERIFICATION_STATUS_OFFSET           (0x14U)
/*! @brief CSE_PRAM offset of the error bits field contained by all commands */
#define FEATURE_CSEC_ERROR_BITS_OFFSET                    (0x4U)
/*! @brief CSE_PRAM offset of the SREG parameter used by the following commands:
CMD_GET_ID */
#define FEATURE_CSEC_SREG_OFFSET                          (0x2FU)

/*! @brief Macro that enables the use of FTFM flash module on a platform */
#define FEATURE_CSEC_HAS_FTFM_MODULE					  (0U)

/*! @brief CSE_PRAM offset of page 0 */
#define FEATURE_CSEC_PAGE_0_OFFSET                        (0x0U)
/*! @brief CSE_PRAM offset of page 1 */
#define FEATURE_CSEC_PAGE_1_OFFSET                        (0x10U)
/*! @brief CSE_PRAM offset of page 2 */
#define FEATURE_CSEC_PAGE_2_OFFSET                        (0x20U)
/*! @brief CSE_PRAM offset of page 3 */
#define FEATURE_CSEC_PAGE_3_OFFSET                        (0x30U)
/*! @brief CSE_PRAM offset of page 4 */
#define FEATURE_CSEC_PAGE_4_OFFSET                        (0x40U)
/*! @brief CSE_PRAM offset of page 5 */
#define FEATURE_CSEC_PAGE_5_OFFSET                        (0x50U)
/*! @brief CSE_PRAM offset of page 6 */
#define FEATURE_CSEC_PAGE_6_OFFSET                        (0x60U)
/*! @brief CSE_PRAM offset of page 7 */
#define FEATURE_CSEC_PAGE_7_OFFSET                        (0x70U)


/* ADC module features */

/*! @brief ADC feature flag for extended number of SC1 and R registers,
 * generically named 'alias registers' */
#define FEATURE_ADC_HAS_EXTRA_NUM_REGS                    (0)

/*! @brief ADC feature flag for defining number of external ADC channels.
 * If each ADC instance has different number of external channels, then
 * this define is set with the maximum value. */
#define FEATURE_ADC_MAX_NUM_EXT_CHANS                     (16)
#define FEATURE_ADC_HAS_CHANNEL_2                         (1)
#define FEATURE_ADC_HAS_CHANNEL_8                         (1)
#define ADC_CLOCKS                                        {ADC0_CLK, ADC1_CLK}

/*! @brief ADC number of control channels */
#if FEATURE_ADC_HAS_EXTRA_NUM_REGS
#define ADC_CTRL_CHANS_COUNT                              ADC_aSC1_COUNT
#else
#define ADC_CTRL_CHANS_COUNT                              ADC_SC1_COUNT
#endif /* FEATURE_ADC_HAS_EXTRA_NUM_REGS */

/*! @brief ADC default Sample Time from RM */
#define ADC_DEFAULT_SAMPLE_TIME                           (0x0CU)
/*! @brief ADC default User Gain from RM */
#define ADC_DEFAULT_USER_GAIN                             (0x04U)
/* @brief Max of adc clock frequency */
#define ADC_CLOCK_FREQ_MAX_RUNTIME     (50000000u)
/* @brief Min of adc clock frequency */
#define ADC_CLOCK_FREQ_MIN_RUNTIME     (2000000u)


/* DMA module features */

/* @brief Number of DMA channels. */
#define FEATURE_DMA_CHANNELS (16U)
/* @brief Number of DMA virtual channels. */
#define FEATURE_DMA_VIRTUAL_CHANNELS (FEATURE_DMA_CHANNELS * DMA_INSTANCE_COUNT)
/* @brief Number of DMA interrupt lines. */
#define FEATURE_DMA_CHANNELS_INTERRUPT_LINES (16U)
/* @brief Number of DMA virtual interrupt lines. */
#define FEATURE_DMA_VIRTUAL_CHANNELS_INTERRUPT_LINES ((uint32_t)FEATURE_DMA_CHANNELS_INTERRUPT_LINES * (uint32_t)DMA_INSTANCE_COUNT)
/* @brief Number of DMA error interrupt lines. */
#define FEATURE_DMA_ERROR_INTERRUPT_LINES (1U)
/* @brief Number of DMA virtual error interrupt lines. */
#define FEATURE_DMA_VIRTUAL_ERROR_INTERRUPT_LINES ((uint32_t)FEATURE_DMA_ERROR_INTERRUPT_LINES * (uint32_t)DMA_INSTANCE_COUNT)
/* @brief DMA module has error interrupt. */
#define FEATURE_DMA_HAS_ERROR_IRQ
/* @brief DMA module separate interrupt lines for each channel */
#define FEATURE_DMA_SEPARATE_IRQ_LINES_PER_CHN
/* @brief Conversion from channel index to DCHPRI index. */
#define FEATURE_DMA_CHN_TO_DCHPRI_INDEX(x) ((x) ^ 3U)
/* @brief DMA channel groups count. */
#define FEATURE_DMA_CHANNEL_GROUP_COUNT (1U)
/* @brief Clock name for DMA */
#define FEATURE_DMA_CLOCK_NAMES {SIM_DMA_CLK}
/* @brief DMA channel width based on number of TCDs: 2^N, N=4,5,... */
#define FEATURE_DMA_CH_WIDTH (4U)
/* @brief DMA channel to instance */
#define FEATURE_DMA_VCH_TO_INSTANCE(x) 	((x) >> (uint32_t)FEATURE_DMA_CH_WIDTH)
/* @brief DMA virtual channel to channel */
#define FEATURE_DMA_VCH_TO_CH(x)        ((x) & ((uint32_t)FEATURE_DMA_CHANNELS - 1U))
/* @brief DMA supports the following particular transfer size: */
#define FEATURE_DMA_TRANSFER_SIZE_16B
#define FEATURE_DMA_TRANSFER_SIZE_32B


/* DMAMUX module features */

/* @brief DMAMUX peripheral is available in silicon. */
#define FEATURE_DMAMUX_AVAILABLE
/* @brief Number of DMA channels. */
#define FEATURE_DMAMUX_CHANNELS (16U)
/* @brief Has the periodic trigger capability */
#define FEATURE_DMAMUX_HAS_TRIG (1)
/* @brief Conversion from request source to the actual DMAMUX channel */
#define FEATURE_DMAMUX_REQ_SRC_TO_CH(x) (x)
/* @brief Mapping between request source and DMAMUX instance */
#define FEATURE_DMAMUX_REQ_SRC_TO_INSTANCE(x) (0U)
/* @brief Conversion from eDMA channel index to DMAMUX channel. */
#define FEATURE_DMAMUX_DMA_CH_TO_CH(x) (x)
/* @brief Conversion from DMAMUX channel DMAMUX register index. */
#define FEATURE_DMAMUX_CHN_REG_INDEX(x) (x)
/* @brief Clock names for DMAMUX. */
#define FEATURE_DMAMUX_CLOCK_NAMES {DMAMUX0_CLK}

#include <stdint.h>

#ifndef __IO
#ifdef __cplusplus
  #define   __I     volatile             /*!< Defines 'read only' permissions                 */
#else
  #define   __I     volatile const       /*!< Defines 'read only' permissions                 */
#endif
#define     __O     volatile             /*!< Defines 'write only' permissions                */
#define     __IO    volatile             /*!< Defines 'read / write' permissions              */
#endif


/* ----------------------------------------------------------------------------
   -- S32_SCB Peripheral Access Layer
   ---------------------------------------------------------------------------- */

/*!
 * @addtogroup S32_SCB_Peripheral_Access_Layer S32_SCB Peripheral Access Layer
 * @{
 */


/** S32_SCB - Size of Registers Arrays */

/** S32_SCB - Register Layout Typedef */
typedef struct {
       uint8_t RESERVED_0[8];
  __IO uint32_t ACTLR;                             /**< Auxiliary Control Register,, offset: 0x8 */
       uint8_t RESERVED_1[3316];
  __I  uint32_t CPUID;                             /**< CPUID Base Register, offset: 0xD00 */
  __IO uint32_t ICSR;                              /**< Interrupt Control and State Register, offset: 0xD04 */
  __IO uint32_t VTOR;                              /**< Vector Table Offset Register, offset: 0xD08 */
  __IO uint32_t AIRCR;                             /**< Application Interrupt and Reset Control Register, offset: 0xD0C */
  __IO uint32_t SCR;                               /**< System Control Register, offset: 0xD10 */
  __IO uint32_t CCR;                               /**< Configuration and Control Register, offset: 0xD14 */
  __IO uint32_t SHPR1;                             /**< System Handler Priority Register 1, offset: 0xD18 */
  __IO uint32_t SHPR2;                             /**< System Handler Priority Register 2, offset: 0xD1C */
  __IO uint32_t SHPR3;                             /**< System Handler Priority Register 3, offset: 0xD20 */
  __IO uint32_t SHCSR;                             /**< System Handler Control and State Register, offset: 0xD24 */
  __IO uint32_t CFSR;                              /**< Configurable Fault Status Registers, offset: 0xD28 */
  __IO uint32_t HFSR;                              /**< HardFault Status register, offset: 0xD2C */
  __IO uint32_t DFSR;                              /**< Debug Fault Status Register, offset: 0xD30 */
  __IO uint32_t MMFAR;                             /**< MemManage Address Register, offset: 0xD34 */
  __IO uint32_t BFAR;                              /**< BusFault Address Register, offset: 0xD38 */
  __IO uint32_t AFSR;                              /**< Auxiliary Fault Status Register, offset: 0xD3C */
       uint8_t RESERVED_2[72];
  __IO uint32_t CPACR;                             /**< Coprocessor Access Control Register, offset: 0xD88 */
       uint8_t RESERVED_3[424];
  __IO uint32_t FPCCR;                             /**< Floating-point Context Control Register, offset: 0xF34 */
  __IO uint32_t FPCAR;                             /**< Floating-point Context Address Register, offset: 0xF38 */
  __IO uint32_t FPDSCR;                            /**< Floating-point Default Status Control Register, offset: 0xF3C */
} S32_SCB_Type, *S32_SCB_MemMapPtr;

 /** Number of instances of the S32_SCB module. */
#define S32_SCB_INSTANCE_COUNT                   (1u)


/* S32_SCB - Peripheral instance base addresses */
/** Peripheral S32_SCB base address */
#define S32_SCB_BASE                             (0xE000E000u)
/** Peripheral S32_SCB base pointer */
#define S32_SCB                                  ((S32_SCB_Type *)S32_SCB_BASE)
/** Array initializer of S32_SCB peripheral base addresses */
#define S32_SCB_BASE_ADDRS                       { S32_SCB_BASE }
/** Array initializer of S32_SCB peripheral base pointers */
#define S32_SCB_BASE_PTRS                        { S32_SCB }

/* ----------------------------------------------------------------------------
   -- S32_SCB Register Masks
   ---------------------------------------------------------------------------- */

/*!
 * @addtogroup S32_SCB_Register_Masks S32_SCB Register Masks
 * @{
 */

/* ACTLR Bit Fields */
#define S32_SCB_ACTLR_DISMCYCINT_MASK            0x1u
#define S32_SCB_ACTLR_DISMCYCINT_SHIFT           0u
#define S32_SCB_ACTLR_DISMCYCINT_WIDTH           1u
#define S32_SCB_ACTLR_DISMCYCINT(x)              (((uint32_t)(((uint32_t)(x))<<S32_SCB_ACTLR_DISMCYCINT_SHIFT))&S32_SCB_ACTLR_DISMCYCINT_MASK)
#define S32_SCB_ACTLR_DISDEFWBUF_MASK            0x2u
#define S32_SCB_ACTLR_DISDEFWBUF_SHIFT           1u
#define S32_SCB_ACTLR_DISDEFWBUF_WIDTH           1u
#define S32_SCB_ACTLR_DISDEFWBUF(x)              (((uint32_t)(((uint32_t)(x))<<S32_SCB_ACTLR_DISDEFWBUF_SHIFT))&S32_SCB_ACTLR_DISDEFWBUF_MASK)
#define S32_SCB_ACTLR_DISFOLD_MASK               0x4u
#define S32_SCB_ACTLR_DISFOLD_SHIFT              2u
#define S32_SCB_ACTLR_DISFOLD_WIDTH              1u
#define S32_SCB_ACTLR_DISFOLD(x)                 (((uint32_t)(((uint32_t)(x))<<S32_SCB_ACTLR_DISFOLD_SHIFT))&S32_SCB_ACTLR_DISFOLD_MASK)
#define S32_SCB_ACTLR_DISFPCA_MASK               0x100u
#define S32_SCB_ACTLR_DISFPCA_SHIFT              8u
#define S32_SCB_ACTLR_DISFPCA_WIDTH              1u
#define S32_SCB_ACTLR_DISFPCA(x)                 (((uint32_t)(((uint32_t)(x))<<S32_SCB_ACTLR_DISFPCA_SHIFT))&S32_SCB_ACTLR_DISFPCA_MASK)
#define S32_SCB_ACTLR_DISOOFP_MASK               0x200u
#define S32_SCB_ACTLR_DISOOFP_SHIFT              9u
#define S32_SCB_ACTLR_DISOOFP_WIDTH              1u
#define S32_SCB_ACTLR_DISOOFP(x)                 (((uint32_t)(((uint32_t)(x))<<S32_SCB_ACTLR_DISOOFP_SHIFT))&S32_SCB_ACTLR_DISOOFP_MASK)
/* CPUID Bit Fields */
#define S32_SCB_CPUID_REVISION_MASK              0xFu
#define S32_SCB_CPUID_REVISION_SHIFT             0u
#define S32_SCB_CPUID_REVISION_WIDTH             4u
#define S32_SCB_CPUID_REVISION(x)                (((uint32_t)(((uint32_t)(x))<<S32_SCB_CPUID_REVISION_SHIFT))&S32_SCB_CPUID_REVISION_MASK)
#define S32_SCB_CPUID_PARTNO_MASK                0xFFF0u
#define S32_SCB_CPUID_PARTNO_SHIFT               4u
#define S32_SCB_CPUID_PARTNO_WIDTH               12u
#define S32_SCB_CPUID_PARTNO(x)                  (((uint32_t)(((uint32_t)(x))<<S32_SCB_CPUID_PARTNO_SHIFT))&S32_SCB_CPUID_PARTNO_MASK)
#define S32_SCB_CPUID_VARIANT_MASK               0xF00000u
#define S32_SCB_CPUID_VARIANT_SHIFT              20u
#define S32_SCB_CPUID_VARIANT_WIDTH              4u
#define S32_SCB_CPUID_VARIANT(x)                 (((uint32_t)(((uint32_t)(x))<<S32_SCB_CPUID_VARIANT_SHIFT))&S32_SCB_CPUID_VARIANT_MASK)
#define S32_SCB_CPUID_IMPLEMENTER_MASK           0xFF000000u
#define S32_SCB_CPUID_IMPLEMENTER_SHIFT          24u
#define S32_SCB_CPUID_IMPLEMENTER_WIDTH          8u
#define S32_SCB_CPUID_IMPLEMENTER(x)             (((uint32_t)(((uint32_t)(x))<<S32_SCB_CPUID_IMPLEMENTER_SHIFT))&S32_SCB_CPUID_IMPLEMENTER_MASK)
/* ICSR Bit Fields */
#define S32_SCB_ICSR_VECTACTIVE_MASK             0x1FFu
#define S32_SCB_ICSR_VECTACTIVE_SHIFT            0u
#define S32_SCB_ICSR_VECTACTIVE_WIDTH            9u
#define S32_SCB_ICSR_VECTACTIVE(x)               (((uint32_t)(((uint32_t)(x))<<S32_SCB_ICSR_VECTACTIVE_SHIFT))&S32_SCB_ICSR_VECTACTIVE_MASK)
#define S32_SCB_ICSR_RETTOBASE_MASK              0x800u
#define S32_SCB_ICSR_RETTOBASE_SHIFT             11u
#define S32_SCB_ICSR_RETTOBASE_WIDTH             1u
#define S32_SCB_ICSR_RETTOBASE(x)                (((uint32_t)(((uint32_t)(x))<<S32_SCB_ICSR_RETTOBASE_SHIFT))&S32_SCB_ICSR_RETTOBASE_MASK)
#define S32_SCB_ICSR_VECTPENDING_MASK            0x3F000u
#define S32_SCB_ICSR_VECTPENDING_SHIFT           12u
#define S32_SCB_ICSR_VECTPENDING_WIDTH           6u
#define S32_SCB_ICSR_VECTPENDING(x)              (((uint32_t)(((uint32_t)(x))<<S32_SCB_ICSR_VECTPENDING_SHIFT))&S32_SCB_ICSR_VECTPENDING_MASK)
#define S32_SCB_ICSR_ISRPENDING_MASK             0x400000u
#define S32_SCB_ICSR_ISRPENDING_SHIFT            22u
#define S32_SCB_ICSR_ISRPENDING_WIDTH            1u
#define S32_SCB_ICSR_ISRPENDING(x)               (((uint32_t)(((uint32_t)(x))<<S32_SCB_ICSR_ISRPENDING_SHIFT))&S32_SCB_ICSR_ISRPENDING_MASK)
#define S32_SCB_ICSR_ISRPREEMPT_MASK             0x800000u
#define S32_SCB_ICSR_ISRPREEMPT_SHIFT            23u
#define S32_SCB_ICSR_ISRPREEMPT_WIDTH            1u
#define S32_SCB_ICSR_ISRPREEMPT(x)               (((uint32_t)(((uint32_t)(x))<<S32_SCB_ICSR_ISRPREEMPT_SHIFT))&S32_SCB_ICSR_ISRPREEMPT_MASK)
#define S32_SCB_ICSR_PENDSTCLR_MASK              0x2000000u
#define S32_SCB_ICSR_PENDSTCLR_SHIFT             25u
#define S32_SCB_ICSR_PENDSTCLR_WIDTH             1u
#define S32_SCB_ICSR_PENDSTCLR(x)                (((uint32_t)(((uint32_t)(x))<<S32_SCB_ICSR_PENDSTCLR_SHIFT))&S32_SCB_ICSR_PENDSTCLR_MASK)
#define S32_SCB_ICSR_PENDSTSET_MASK              0x4000000u
#define S32_SCB_ICSR_PENDSTSET_SHIFT             26u
#define S32_SCB_ICSR_PENDSTSET_WIDTH             1u
#define S32_SCB_ICSR_PENDSTSET(x)                (((uint32_t)(((uint32_t)(x))<<S32_SCB_ICSR_PENDSTSET_SHIFT))&S32_SCB_ICSR_PENDSTSET_MASK)
#define S32_SCB_ICSR_PENDSVCLR_MASK              0x8000000u
#define S32_SCB_ICSR_PENDSVCLR_SHIFT             27u
#define S32_SCB_ICSR_PENDSVCLR_WIDTH             1u
#define S32_SCB_ICSR_PENDSVCLR(x)                (((uint32_t)(((uint32_t)(x))<<S32_SCB_ICSR_PENDSVCLR_SHIFT))&S32_SCB_ICSR_PENDSVCLR_MASK)
#define S32_SCB_ICSR_PENDSVSET_MASK              0x10000000u
#define S32_SCB_ICSR_PENDSVSET_SHIFT             28u
#define S32_SCB_ICSR_PENDSVSET_WIDTH             1u
#define S32_SCB_ICSR_PENDSVSET(x)                (((uint32_t)(((uint32_t)(x))<<S32_SCB_ICSR_PENDSVSET_SHIFT))&S32_SCB_ICSR_PENDSVSET_MASK)
#define S32_SCB_ICSR_NMIPENDSET_MASK             0x80000000u
#define S32_SCB_ICSR_NMIPENDSET_SHIFT            31u
#define S32_SCB_ICSR_NMIPENDSET_WIDTH            1u
#define S32_SCB_ICSR_NMIPENDSET(x)               (((uint32_t)(((uint32_t)(x))<<S32_SCB_ICSR_NMIPENDSET_SHIFT))&S32_SCB_ICSR_NMIPENDSET_MASK)
/* VTOR Bit Fields */
#define S32_SCB_VTOR_TBLOFF_MASK                 0xFFFFFF80u
#define S32_SCB_VTOR_TBLOFF_SHIFT                7u
#define S32_SCB_VTOR_TBLOFF_WIDTH                25u
#define S32_SCB_VTOR_TBLOFF(x)                   (((uint32_t)(((uint32_t)(x))<<S32_SCB_VTOR_TBLOFF_SHIFT))&S32_SCB_VTOR_TBLOFF_MASK)
/* AIRCR Bit Fields */
#define S32_SCB_AIRCR_VECTRESET_MASK             0x1u
#define S32_SCB_AIRCR_VECTRESET_SHIFT            0u
#define S32_SCB_AIRCR_VECTRESET_WIDTH            1u
#define S32_SCB_AIRCR_VECTRESET(x)               (((uint32_t)(((uint32_t)(x))<<S32_SCB_AIRCR_VECTRESET_SHIFT))&S32_SCB_AIRCR_VECTRESET_MASK)
#define S32_SCB_AIRCR_VECTCLRACTIVE_MASK         0x2u
#define S32_SCB_AIRCR_VECTCLRACTIVE_SHIFT        1u
#define S32_SCB_AIRCR_VECTCLRACTIVE_WIDTH        1u
#define S32_SCB_AIRCR_VECTCLRACTIVE(x)           (((uint32_t)(((uint32_t)(x))<<S32_SCB_AIRCR_VECTCLRACTIVE_SHIFT))&S32_SCB_AIRCR_VECTCLRACTIVE_MASK)
#define S32_SCB_AIRCR_SYSRESETREQ_MASK           0x4u
#define S32_SCB_AIRCR_SYSRESETREQ_SHIFT          2u
#define S32_SCB_AIRCR_SYSRESETREQ_WIDTH          1u
#define S32_SCB_AIRCR_SYSRESETREQ(x)             (((uint32_t)(((uint32_t)(x))<<S32_SCB_AIRCR_SYSRESETREQ_SHIFT))&S32_SCB_AIRCR_SYSRESETREQ_MASK)
#define S32_SCB_AIRCR_PRIGROUP_MASK              0x700u
#define S32_SCB_AIRCR_PRIGROUP_SHIFT             8u
#define S32_SCB_AIRCR_PRIGROUP_WIDTH             3u
#define S32_SCB_AIRCR_PRIGROUP(x)                (((uint32_t)(((uint32_t)(x))<<S32_SCB_AIRCR_PRIGROUP_SHIFT))&S32_SCB_AIRCR_PRIGROUP_MASK)
#define S32_SCB_AIRCR_ENDIANNESS_MASK            0x8000u
#define S32_SCB_AIRCR_ENDIANNESS_SHIFT           15u
#define S32_SCB_AIRCR_ENDIANNESS_WIDTH           1u
#define S32_SCB_AIRCR_ENDIANNESS(x)              (((uint32_t)(((uint32_t)(x))<<S32_SCB_AIRCR_ENDIANNESS_SHIFT))&S32_SCB_AIRCR_ENDIANNESS_MASK)
#define S32_SCB_AIRCR_VECTKEY_MASK               0xFFFF0000u
#define S32_SCB_AIRCR_VECTKEY_SHIFT              16u
#define S32_SCB_AIRCR_VECTKEY_WIDTH              16u
#define S32_SCB_AIRCR_VECTKEY(x)                 (((uint32_t)(((uint32_t)(x))<<S32_SCB_AIRCR_VECTKEY_SHIFT))&S32_SCB_AIRCR_VECTKEY_MASK)
/* SCR Bit Fields */
#define S32_SCB_SCR_SLEEPONEXIT_MASK             0x2u
#define S32_SCB_SCR_SLEEPONEXIT_SHIFT            1u
#define S32_SCB_SCR_SLEEPONEXIT_WIDTH            1u
#define S32_SCB_SCR_SLEEPONEXIT(x)               (((uint32_t)(((uint32_t)(x))<<S32_SCB_SCR_SLEEPONEXIT_SHIFT))&S32_SCB_SCR_SLEEPONEXIT_MASK)
#define S32_SCB_SCR_SLEEPDEEP_MASK               0x4u
#define S32_SCB_SCR_SLEEPDEEP_SHIFT              2u
#define S32_SCB_SCR_SLEEPDEEP_WIDTH              1u
#define S32_SCB_SCR_SLEEPDEEP(x)                 (((uint32_t)(((uint32_t)(x))<<S32_SCB_SCR_SLEEPDEEP_SHIFT))&S32_SCB_SCR_SLEEPDEEP_MASK)
#define S32_SCB_SCR_SEVONPEND_MASK               0x10u
#define S32_SCB_SCR_SEVONPEND_SHIFT              4u
#define S32_SCB_SCR_SEVONPEND_WIDTH              1u
#define S32_SCB_SCR_SEVONPEND(x)                 (((uint32_t)(((uint32_t)(x))<<S32_SCB_SCR_SEVONPEND_SHIFT))&S32_SCB_SCR_SEVONPEND_MASK)
/* CCR Bit Fields */
#define S32_SCB_CCR_NONBASETHRDENA_MASK          0x1u
#define S32_SCB_CCR_NONBASETHRDENA_SHIFT         0u
#define S32_SCB_CCR_NONBASETHRDENA_WIDTH         1u
#define S32_SCB_CCR_NONBASETHRDENA(x)            (((uint32_t)(((uint32_t)(x))<<S32_SCB_CCR_NONBASETHRDENA_SHIFT))&S32_SCB_CCR_NONBASETHRDENA_MASK)
#define S32_SCB_CCR_USERSETMPEND_MASK            0x2u
#define S32_SCB_CCR_USERSETMPEND_SHIFT           1u
#define S32_SCB_CCR_USERSETMPEND_WIDTH           1u
#define S32_SCB_CCR_USERSETMPEND(x)              (((uint32_t)(((uint32_t)(x))<<S32_SCB_CCR_USERSETMPEND_SHIFT))&S32_SCB_CCR_USERSETMPEND_MASK)
#define S32_SCB_CCR_UNALIGN_TRP_MASK             0x8u
#define S32_SCB_CCR_UNALIGN_TRP_SHIFT            3u
#define S32_SCB_CCR_UNALIGN_TRP_WIDTH            1u
#define S32_SCB_CCR_UNALIGN_TRP(x)               (((uint32_t)(((uint32_t)(x))<<S32_SCB_CCR_UNALIGN_TRP_SHIFT))&S32_SCB_CCR_UNALIGN_TRP_MASK)
#define S32_SCB_CCR_DIV_0_TRP_MASK               0x10u
#define S32_SCB_CCR_DIV_0_TRP_SHIFT              4u
#define S32_SCB_CCR_DIV_0_TRP_WIDTH              1u
#define S32_SCB_CCR_DIV_0_TRP(x)                 (((uint32_t)(((uint32_t)(x))<<S32_SCB_CCR_DIV_0_TRP_SHIFT))&S32_SCB_CCR_DIV_0_TRP_MASK)
#define S32_SCB_CCR_BFHFNMIGN_MASK               0x100u
#define S32_SCB_CCR_BFHFNMIGN_SHIFT              8u
#define S32_SCB_CCR_BFHFNMIGN_WIDTH              1u
#define S32_SCB_CCR_BFHFNMIGN(x)                 (((uint32_t)(((uint32_t)(x))<<S32_SCB_CCR_BFHFNMIGN_SHIFT))&S32_SCB_CCR_BFHFNMIGN_MASK)
#define S32_SCB_CCR_STKALIGN_MASK                0x200u
#define S32_SCB_CCR_STKALIGN_SHIFT               9u
#define S32_SCB_CCR_STKALIGN_WIDTH               1u
#define S32_SCB_CCR_STKALIGN(x)                  (((uint32_t)(((uint32_t)(x))<<S32_SCB_CCR_STKALIGN_SHIFT))&S32_SCB_CCR_STKALIGN_MASK)
/* SHPR1 Bit Fields */
#define S32_SCB_SHPR1_PRI_4_MASK                 0xFFu
#define S32_SCB_SHPR1_PRI_4_SHIFT                0u
#define S32_SCB_SHPR1_PRI_4_WIDTH                8u
#define S32_SCB_SHPR1_PRI_4(x)                   (((uint32_t)(((uint32_t)(x))<<S32_SCB_SHPR1_PRI_4_SHIFT))&S32_SCB_SHPR1_PRI_4_MASK)
#define S32_SCB_SHPR1_PRI_5_MASK                 0xFF00u
#define S32_SCB_SHPR1_PRI_5_SHIFT                8u
#define S32_SCB_SHPR1_PRI_5_WIDTH                8u
#define S32_SCB_SHPR1_PRI_5(x)                   (((uint32_t)(((uint32_t)(x))<<S32_SCB_SHPR1_PRI_5_SHIFT))&S32_SCB_SHPR1_PRI_5_MASK)
#define S32_SCB_SHPR1_PRI_6_MASK                 0xFF0000u
#define S32_SCB_SHPR1_PRI_6_SHIFT                16u
#define S32_SCB_SHPR1_PRI_6_WIDTH                8u
#define S32_SCB_SHPR1_PRI_6(x)                   (((uint32_t)(((uint32_t)(x))<<S32_SCB_SHPR1_PRI_6_SHIFT))&S32_SCB_SHPR1_PRI_6_MASK)
/* SHPR2 Bit Fields */
#define S32_SCB_SHPR2_PRI_11_MASK                0xFF000000u
#define S32_SCB_SHPR2_PRI_11_SHIFT               24u
#define S32_SCB_SHPR2_PRI_11_WIDTH               8u
#define S32_SCB_SHPR2_PRI_11(x)                  (((uint32_t)(((uint32_t)(x))<<S32_SCB_SHPR2_PRI_11_SHIFT))&S32_SCB_SHPR2_PRI_11_MASK)
/* SHPR3 Bit Fields */
#define S32_SCB_SHPR3_PRI_12_MASK                0xFFu
#define S32_SCB_SHPR3_PRI_12_SHIFT               0u
#define S32_SCB_SHPR3_PRI_12_WIDTH               8u
#define S32_SCB_SHPR3_PRI_12(x)                  (((uint32_t)(((uint32_t)(x))<<S32_SCB_SHPR3_PRI_12_SHIFT))&S32_SCB_SHPR3_PRI_12_MASK)
#define S32_SCB_SHPR3_PRI_14_MASK                0xFF0000u
#define S32_SCB_SHPR3_PRI_14_SHIFT               16u
#define S32_SCB_SHPR3_PRI_14_WIDTH               8u
#define S32_SCB_SHPR3_PRI_14(x)                  (((uint32_t)(((uint32_t)(x))<<S32_SCB_SHPR3_PRI_14_SHIFT))&S32_SCB_SHPR3_PRI_14_MASK)
#define S32_SCB_SHPR3_PRI_15_MASK                0xFF000000u
#define S32_SCB_SHPR3_PRI_15_SHIFT               24u
#define S32_SCB_SHPR3_PRI_15_WIDTH               8u
#define S32_SCB_SHPR3_PRI_15(x)                  (((uint32_t)(((uint32_t)(x))<<S32_SCB_SHPR3_PRI_15_SHIFT))&S32_SCB_SHPR3_PRI_15_MASK)
/* SHCSR Bit Fields */
#define S32_SCB_SHCSR_MEMFAULTACT_MASK           0x1u
#define S32_SCB_SHCSR_MEMFAULTACT_SHIFT          0u
#define S32_SCB_SHCSR_MEMFAULTACT_WIDTH          1u
#define S32_SCB_SHCSR_MEMFAULTACT(x)             (((uint32_t)(((uint32_t)(x))<<S32_SCB_SHCSR_MEMFAULTACT_SHIFT))&S32_SCB_SHCSR_MEMFAULTACT_MASK)
#define S32_SCB_SHCSR_BUSFAULTACT_MASK           0x2u
#define S32_SCB_SHCSR_BUSFAULTACT_SHIFT          1u
#define S32_SCB_SHCSR_BUSFAULTACT_WIDTH          1u
#define S32_SCB_SHCSR_BUSFAULTACT(x)             (((uint32_t)(((uint32_t)(x))<<S32_SCB_SHCSR_BUSFAULTACT_SHIFT))&S32_SCB_SHCSR_BUSFAULTACT_MASK)
#define S32_SCB_SHCSR_USGFAULTACT_MASK           0x8u
#define S32_SCB_SHCSR_USGFAULTACT_SHIFT          3u
#define S32_SCB_SHCSR_USGFAULTACT_WIDTH          1u
#define S32_SCB_SHCSR_USGFAULTACT(x)             (((uint32_t)(((uint32_t)(x))<<S32_SCB_SHCSR_USGFAULTACT_SHIFT))&S32_SCB_SHCSR_USGFAULTACT_MASK)
#define S32_SCB_SHCSR_SVCALLACT_MASK             0x80u
#define S32_SCB_SHCSR_SVCALLACT_SHIFT            7u
#define S32_SCB_SHCSR_SVCALLACT_WIDTH            1u
#define S32_SCB_SHCSR_SVCALLACT(x)               (((uint32_t)(((uint32_t)(x))<<S32_SCB_SHCSR_SVCALLACT_SHIFT))&S32_SCB_SHCSR_SVCALLACT_MASK)
#define S32_SCB_SHCSR_MONITORACT_MASK            0x100u
#define S32_SCB_SHCSR_MONITORACT_SHIFT           8u
#define S32_SCB_SHCSR_MONITORACT_WIDTH           1u
#define S32_SCB_SHCSR_MONITORACT(x)              (((uint32_t)(((uint32_t)(x))<<S32_SCB_SHCSR_MONITORACT_SHIFT))&S32_SCB_SHCSR_MONITORACT_MASK)
#define S32_SCB_SHCSR_PENDSVACT_MASK             0x400u
#define S32_SCB_SHCSR_PENDSVACT_SHIFT            10u
#define S32_SCB_SHCSR_PENDSVACT_WIDTH            1u
#define S32_SCB_SHCSR_PENDSVACT(x)               (((uint32_t)(((uint32_t)(x))<<S32_SCB_SHCSR_PENDSVACT_SHIFT))&S32_SCB_SHCSR_PENDSVACT_MASK)
#define S32_SCB_SHCSR_SYSTICKACT_MASK            0x800u
#define S32_SCB_SHCSR_SYSTICKACT_SHIFT           11u
#define S32_SCB_SHCSR_SYSTICKACT_WIDTH           1u
#define S32_SCB_SHCSR_SYSTICKACT(x)              (((uint32_t)(((uint32_t)(x))<<S32_SCB_SHCSR_SYSTICKACT_SHIFT))&S32_SCB_SHCSR_SYSTICKACT_MASK)
#define S32_SCB_SHCSR_USGFAULTPENDED_MASK        0x1000u
#define S32_SCB_SHCSR_USGFAULTPENDED_SHIFT       12u
#define S32_SCB_SHCSR_USGFAULTPENDED_WIDTH       1u
#define S32_SCB_SHCSR_USGFAULTPENDED(x)          (((uint32_t)(((uint32_t)(x))<<S32_SCB_SHCSR_USGFAULTPENDED_SHIFT))&S32_SCB_SHCSR_USGFAULTPENDED_MASK)
#define S32_SCB_SHCSR_MEMFAULTPENDED_MASK        0x2000u
#define S32_SCB_SHCSR_MEMFAULTPENDED_SHIFT       13u
#define S32_SCB_SHCSR_MEMFAULTPENDED_WIDTH       1u
#define S32_SCB_SHCSR_MEMFAULTPENDED(x)          (((uint32_t)(((uint32_t)(x))<<S32_SCB_SHCSR_MEMFAULTPENDED_SHIFT))&S32_SCB_SHCSR_MEMFAULTPENDED_MASK)
#define S32_SCB_SHCSR_BUSFAULTPENDED_MASK        0x4000u
#define S32_SCB_SHCSR_BUSFAULTPENDED_SHIFT       14u
#define S32_SCB_SHCSR_BUSFAULTPENDED_WIDTH       1u
#define S32_SCB_SHCSR_BUSFAULTPENDED(x)          (((uint32_t)(((uint32_t)(x))<<S32_SCB_SHCSR_BUSFAULTPENDED_SHIFT))&S32_SCB_SHCSR_BUSFAULTPENDED_MASK)
#define S32_SCB_SHCSR_SVCALLPENDED_MASK          0x8000u
#define S32_SCB_SHCSR_SVCALLPENDED_SHIFT         15u
#define S32_SCB_SHCSR_SVCALLPENDED_WIDTH         1u
#define S32_SCB_SHCSR_SVCALLPENDED(x)            (((uint32_t)(((uint32_t)(x))<<S32_SCB_SHCSR_SVCALLPENDED_SHIFT))&S32_SCB_SHCSR_SVCALLPENDED_MASK)
#define S32_SCB_SHCSR_MEMFAULTENA_MASK           0x10000u
#define S32_SCB_SHCSR_MEMFAULTENA_SHIFT          16u
#define S32_SCB_SHCSR_MEMFAULTENA_WIDTH          1u
#define S32_SCB_SHCSR_MEMFAULTENA(x)             (((uint32_t)(((uint32_t)(x))<<S32_SCB_SHCSR_MEMFAULTENA_SHIFT))&S32_SCB_SHCSR_MEMFAULTENA_MASK)
#define S32_SCB_SHCSR_BUSFAULTENA_MASK           0x20000u
#define S32_SCB_SHCSR_BUSFAULTENA_SHIFT          17u
#define S32_SCB_SHCSR_BUSFAULTENA_WIDTH          1u
#define S32_SCB_SHCSR_BUSFAULTENA(x)             (((uint32_t)(((uint32_t)(x))<<S32_SCB_SHCSR_BUSFAULTENA_SHIFT))&S32_SCB_SHCSR_BUSFAULTENA_MASK)
#define S32_SCB_SHCSR_USGFAULTENA_MASK           0x40000u
#define S32_SCB_SHCSR_USGFAULTENA_SHIFT          18u
#define S32_SCB_SHCSR_USGFAULTENA_WIDTH          1u
#define S32_SCB_SHCSR_USGFAULTENA(x)             (((uint32_t)(((uint32_t)(x))<<S32_SCB_SHCSR_USGFAULTENA_SHIFT))&S32_SCB_SHCSR_USGFAULTENA_MASK)
/* CFSR Bit Fields */
#define S32_SCB_CFSR_IACCVIOL_MASK               0x1u
#define S32_SCB_CFSR_IACCVIOL_SHIFT              0u
#define S32_SCB_CFSR_IACCVIOL_WIDTH              1u
#define S32_SCB_CFSR_IACCVIOL(x)                 (((uint32_t)(((uint32_t)(x))<<S32_SCB_CFSR_IACCVIOL_SHIFT))&S32_SCB_CFSR_IACCVIOL_MASK)
#define S32_SCB_CFSR_DACCVIOL_MASK               0x2u
#define S32_SCB_CFSR_DACCVIOL_SHIFT              1u
#define S32_SCB_CFSR_DACCVIOL_WIDTH              1u
#define S32_SCB_CFSR_DACCVIOL(x)                 (((uint32_t)(((uint32_t)(x))<<S32_SCB_CFSR_DACCVIOL_SHIFT))&S32_SCB_CFSR_DACCVIOL_MASK)
#define S32_SCB_CFSR_MUNSTKERR_MASK              0x8u
#define S32_SCB_CFSR_MUNSTKERR_SHIFT             3u
#define S32_SCB_CFSR_MUNSTKERR_WIDTH             1u
#define S32_SCB_CFSR_MUNSTKERR(x)                (((uint32_t)(((uint32_t)(x))<<S32_SCB_CFSR_MUNSTKERR_SHIFT))&S32_SCB_CFSR_MUNSTKERR_MASK)
#define S32_SCB_CFSR_MSTKERR_MASK                0x10u
#define S32_SCB_CFSR_MSTKERR_SHIFT               4u
#define S32_SCB_CFSR_MSTKERR_WIDTH               1u
#define S32_SCB_CFSR_MSTKERR(x)                  (((uint32_t)(((uint32_t)(x))<<S32_SCB_CFSR_MSTKERR_SHIFT))&S32_SCB_CFSR_MSTKERR_MASK)
#define S32_SCB_CFSR_MLSPERR_MASK                0x20u
#define S32_SCB_CFSR_MLSPERR_SHIFT               5u
#define S32_SCB_CFSR_MLSPERR_WIDTH               1u
#define S32_SCB_CFSR_MLSPERR(x)                  (((uint32_t)(((uint32_t)(x))<<S32_SCB_CFSR_MLSPERR_SHIFT))&S32_SCB_CFSR_MLSPERR_MASK)
#define S32_SCB_CFSR_MMARVALID_MASK              0x80u
#define S32_SCB_CFSR_MMARVALID_SHIFT             7u
#define S32_SCB_CFSR_MMARVALID_WIDTH             1u
#define S32_SCB_CFSR_MMARVALID(x)                (((uint32_t)(((uint32_t)(x))<<S32_SCB_CFSR_MMARVALID_SHIFT))&S32_SCB_CFSR_MMARVALID_MASK)
#define S32_SCB_CFSR_IBUSERR_MASK                0x100u
#define S32_SCB_CFSR_IBUSERR_SHIFT               8u
#define S32_SCB_CFSR_IBUSERR_WIDTH               1u
#define S32_SCB_CFSR_IBUSERR(x)                  (((uint32_t)(((uint32_t)(x))<<S32_SCB_CFSR_IBUSERR_SHIFT))&S32_SCB_CFSR_IBUSERR_MASK)
#define S32_SCB_CFSR_PRECISERR_MASK              0x200u
#define S32_SCB_CFSR_PRECISERR_SHIFT             9u
#define S32_SCB_CFSR_PRECISERR_WIDTH             1u
#define S32_SCB_CFSR_PRECISERR(x)                (((uint32_t)(((uint32_t)(x))<<S32_SCB_CFSR_PRECISERR_SHIFT))&S32_SCB_CFSR_PRECISERR_MASK)
#define S32_SCB_CFSR_IMPRECISERR_MASK            0x400u
#define S32_SCB_CFSR_IMPRECISERR_SHIFT           10u
#define S32_SCB_CFSR_IMPRECISERR_WIDTH           1u
#define S32_SCB_CFSR_IMPRECISERR(x)              (((uint32_t)(((uint32_t)(x))<<S32_SCB_CFSR_IMPRECISERR_SHIFT))&S32_SCB_CFSR_IMPRECISERR_MASK)
#define S32_SCB_CFSR_UNSTKERR_MASK               0x800u
#define S32_SCB_CFSR_UNSTKERR_SHIFT              11u
#define S32_SCB_CFSR_UNSTKERR_WIDTH              1u
#define S32_SCB_CFSR_UNSTKERR(x)                 (((uint32_t)(((uint32_t)(x))<<S32_SCB_CFSR_UNSTKERR_SHIFT))&S32_SCB_CFSR_UNSTKERR_MASK)
#define S32_SCB_CFSR_STKERR_MASK                 0x1000u
#define S32_SCB_CFSR_STKERR_SHIFT                12u
#define S32_SCB_CFSR_STKERR_WIDTH                1u
#define S32_SCB_CFSR_STKERR(x)                   (((uint32_t)(((uint32_t)(x))<<S32_SCB_CFSR_STKERR_SHIFT))&S32_SCB_CFSR_STKERR_MASK)
#define S32_SCB_CFSR_LSPERR_MASK                 0x2000u
#define S32_SCB_CFSR_LSPERR_SHIFT                13u
#define S32_SCB_CFSR_LSPERR_WIDTH                1u
#define S32_SCB_CFSR_LSPERR(x)                   (((uint32_t)(((uint32_t)(x))<<S32_SCB_CFSR_LSPERR_SHIFT))&S32_SCB_CFSR_LSPERR_MASK)
#define S32_SCB_CFSR_BFARVALID_MASK              0x8000u
#define S32_SCB_CFSR_BFARVALID_SHIFT             15u
#define S32_SCB_CFSR_BFARVALID_WIDTH             1u
#define S32_SCB_CFSR_BFARVALID(x)                (((uint32_t)(((uint32_t)(x))<<S32_SCB_CFSR_BFARVALID_SHIFT))&S32_SCB_CFSR_BFARVALID_MASK)
#define S32_SCB_CFSR_UNDEFINSTR_MASK             0x10000u
#define S32_SCB_CFSR_UNDEFINSTR_SHIFT            16u
#define S32_SCB_CFSR_UNDEFINSTR_WIDTH            1u
#define S32_SCB_CFSR_UNDEFINSTR(x)               (((uint32_t)(((uint32_t)(x))<<S32_SCB_CFSR_UNDEFINSTR_SHIFT))&S32_SCB_CFSR_UNDEFINSTR_MASK)
#define S32_SCB_CFSR_INVSTATE_MASK               0x20000u
#define S32_SCB_CFSR_INVSTATE_SHIFT              17u
#define S32_SCB_CFSR_INVSTATE_WIDTH              1u
#define S32_SCB_CFSR_INVSTATE(x)                 (((uint32_t)(((uint32_t)(x))<<S32_SCB_CFSR_INVSTATE_SHIFT))&S32_SCB_CFSR_INVSTATE_MASK)
#define S32_SCB_CFSR_INVPC_MASK                  0x40000u
#define S32_SCB_CFSR_INVPC_SHIFT                 18u
#define S32_SCB_CFSR_INVPC_WIDTH                 1u
#define S32_SCB_CFSR_INVPC(x)                    (((uint32_t)(((uint32_t)(x))<<S32_SCB_CFSR_INVPC_SHIFT))&S32_SCB_CFSR_INVPC_MASK)
#define S32_SCB_CFSR_NOCP_MASK                   0x80000u
#define S32_SCB_CFSR_NOCP_SHIFT                  19u
#define S32_SCB_CFSR_NOCP_WIDTH                  1u
#define S32_SCB_CFSR_NOCP(x)                     (((uint32_t)(((uint32_t)(x))<<S32_SCB_CFSR_NOCP_SHIFT))&S32_SCB_CFSR_NOCP_MASK)
#define S32_SCB_CFSR_UNALIGNED_MASK              0x1000000u
#define S32_SCB_CFSR_UNALIGNED_SHIFT             24u
#define S32_SCB_CFSR_UNALIGNED_WIDTH             1u
#define S32_SCB_CFSR_UNALIGNED(x)                (((uint32_t)(((uint32_t)(x))<<S32_SCB_CFSR_UNALIGNED_SHIFT))&S32_SCB_CFSR_UNALIGNED_MASK)
#define S32_SCB_CFSR_DIVBYZERO_MASK              0x2000000u
#define S32_SCB_CFSR_DIVBYZERO_SHIFT             25u
#define S32_SCB_CFSR_DIVBYZERO_WIDTH             1u
#define S32_SCB_CFSR_DIVBYZERO(x)                (((uint32_t)(((uint32_t)(x))<<S32_SCB_CFSR_DIVBYZERO_SHIFT))&S32_SCB_CFSR_DIVBYZERO_MASK)
/* HFSR Bit Fields */
#define S32_SCB_HFSR_VECTTBL_MASK                0x2u
#define S32_SCB_HFSR_VECTTBL_SHIFT               1u
#define S32_SCB_HFSR_VECTTBL_WIDTH               1u
#define S32_SCB_HFSR_VECTTBL(x)                  (((uint32_t)(((uint32_t)(x))<<S32_SCB_HFSR_VECTTBL_SHIFT))&S32_SCB_HFSR_VECTTBL_MASK)
#define S32_SCB_HFSR_FORCED_MASK                 0x40000000u
#define S32_SCB_HFSR_FORCED_SHIFT                30u
#define S32_SCB_HFSR_FORCED_WIDTH                1u
#define S32_SCB_HFSR_FORCED(x)                   (((uint32_t)(((uint32_t)(x))<<S32_SCB_HFSR_FORCED_SHIFT))&S32_SCB_HFSR_FORCED_MASK)
#define S32_SCB_HFSR_DEBUGEVT_MASK               0x80000000u
#define S32_SCB_HFSR_DEBUGEVT_SHIFT              31u
#define S32_SCB_HFSR_DEBUGEVT_WIDTH              1u
#define S32_SCB_HFSR_DEBUGEVT(x)                 (((uint32_t)(((uint32_t)(x))<<S32_SCB_HFSR_DEBUGEVT_SHIFT))&S32_SCB_HFSR_DEBUGEVT_MASK)
/* DFSR Bit Fields */
#define S32_SCB_DFSR_HALTED_MASK                 0x1u
#define S32_SCB_DFSR_HALTED_SHIFT                0u
#define S32_SCB_DFSR_HALTED_WIDTH                1u
#define S32_SCB_DFSR_HALTED(x)                   (((uint32_t)(((uint32_t)(x))<<S32_SCB_DFSR_HALTED_SHIFT))&S32_SCB_DFSR_HALTED_MASK)
#define S32_SCB_DFSR_BKPT_MASK                   0x2u
#define S32_SCB_DFSR_BKPT_SHIFT                  1u
#define S32_SCB_DFSR_BKPT_WIDTH                  1u
#define S32_SCB_DFSR_BKPT(x)                     (((uint32_t)(((uint32_t)(x))<<S32_SCB_DFSR_BKPT_SHIFT))&S32_SCB_DFSR_BKPT_MASK)
#define S32_SCB_DFSR_DWTTRAP_MASK                0x4u
#define S32_SCB_DFSR_DWTTRAP_SHIFT               2u
#define S32_SCB_DFSR_DWTTRAP_WIDTH               1u
#define S32_SCB_DFSR_DWTTRAP(x)                  (((uint32_t)(((uint32_t)(x))<<S32_SCB_DFSR_DWTTRAP_SHIFT))&S32_SCB_DFSR_DWTTRAP_MASK)
#define S32_SCB_DFSR_VCATCH_MASK                 0x8u
#define S32_SCB_DFSR_VCATCH_SHIFT                3u
#define S32_SCB_DFSR_VCATCH_WIDTH                1u
#define S32_SCB_DFSR_VCATCH(x)                   (((uint32_t)(((uint32_t)(x))<<S32_SCB_DFSR_VCATCH_SHIFT))&S32_SCB_DFSR_VCATCH_MASK)
#define S32_SCB_DFSR_EXTERNAL_MASK               0x10u
#define S32_SCB_DFSR_EXTERNAL_SHIFT              4u
#define S32_SCB_DFSR_EXTERNAL_WIDTH              1u
#define S32_SCB_DFSR_EXTERNAL(x)                 (((uint32_t)(((uint32_t)(x))<<S32_SCB_DFSR_EXTERNAL_SHIFT))&S32_SCB_DFSR_EXTERNAL_MASK)
/* MMFAR Bit Fields */
#define S32_SCB_MMFAR_ADDRESS_MASK               0xFFFFFFFFu
#define S32_SCB_MMFAR_ADDRESS_SHIFT              0u
#define S32_SCB_MMFAR_ADDRESS_WIDTH              32u
#define S32_SCB_MMFAR_ADDRESS(x)                 (((uint32_t)(((uint32_t)(x))<<S32_SCB_MMFAR_ADDRESS_SHIFT))&S32_SCB_MMFAR_ADDRESS_MASK)
/* BFAR Bit Fields */
#define S32_SCB_BFAR_ADDRESS_MASK                0xFFFFFFFFu
#define S32_SCB_BFAR_ADDRESS_SHIFT               0u
#define S32_SCB_BFAR_ADDRESS_WIDTH               32u
#define S32_SCB_BFAR_ADDRESS(x)                  (((uint32_t)(((uint32_t)(x))<<S32_SCB_BFAR_ADDRESS_SHIFT))&S32_SCB_BFAR_ADDRESS_MASK)
/* AFSR Bit Fields */
#define S32_SCB_AFSR_AUXFAULT_MASK               0xFFFFFFFFu
#define S32_SCB_AFSR_AUXFAULT_SHIFT              0u
#define S32_SCB_AFSR_AUXFAULT_WIDTH              32u
#define S32_SCB_AFSR_AUXFAULT(x)                 (((uint32_t)(((uint32_t)(x))<<S32_SCB_AFSR_AUXFAULT_SHIFT))&S32_SCB_AFSR_AUXFAULT_MASK)
/* CPACR Bit Fields */
#define S32_SCB_CPACR_CP10_MASK                  0x300000u
#define S32_SCB_CPACR_CP10_SHIFT                 20u
#define S32_SCB_CPACR_CP10_WIDTH                 2u
#define S32_SCB_CPACR_CP10(x)                    (((uint32_t)(((uint32_t)(x))<<S32_SCB_CPACR_CP10_SHIFT))&S32_SCB_CPACR_CP10_MASK)
#define S32_SCB_CPACR_CP11_MASK                  0xC00000u
#define S32_SCB_CPACR_CP11_SHIFT                 22u
#define S32_SCB_CPACR_CP11_WIDTH                 2u
#define S32_SCB_CPACR_CP11(x)                    (((uint32_t)(((uint32_t)(x))<<S32_SCB_CPACR_CP11_SHIFT))&S32_SCB_CPACR_CP11_MASK)
/* FPCCR Bit Fields */
#define S32_SCB_FPCCR_LSPACT_MASK                0x1u
#define S32_SCB_FPCCR_LSPACT_SHIFT               0u
#define S32_SCB_FPCCR_LSPACT_WIDTH               1u
#define S32_SCB_FPCCR_LSPACT(x)                  (((uint32_t)(((uint32_t)(x))<<S32_SCB_FPCCR_LSPACT_SHIFT))&S32_SCB_FPCCR_LSPACT_MASK)
#define S32_SCB_FPCCR_USER_MASK                  0x2u
#define S32_SCB_FPCCR_USER_SHIFT                 1u
#define S32_SCB_FPCCR_USER_WIDTH                 1u
#define S32_SCB_FPCCR_USER(x)                    (((uint32_t)(((uint32_t)(x))<<S32_SCB_FPCCR_USER_SHIFT))&S32_SCB_FPCCR_USER_MASK)
#define S32_SCB_FPCCR_THREAD_MASK                0x8u
#define S32_SCB_FPCCR_THREAD_SHIFT               3u
#define S32_SCB_FPCCR_THREAD_WIDTH               1u
#define S32_SCB_FPCCR_THREAD(x)                  (((uint32_t)(((uint32_t)(x))<<S32_SCB_FPCCR_THREAD_SHIFT))&S32_SCB_FPCCR_THREAD_MASK)
#define S32_SCB_FPCCR_HFRDY_MASK                 0x10u
#define S32_SCB_FPCCR_HFRDY_SHIFT                4u
#define S32_SCB_FPCCR_HFRDY_WIDTH                1u
#define S32_SCB_FPCCR_HFRDY(x)                   (((uint32_t)(((uint32_t)(x))<<S32_SCB_FPCCR_HFRDY_SHIFT))&S32_SCB_FPCCR_HFRDY_MASK)
#define S32_SCB_FPCCR_MMRDY_MASK                 0x20u
#define S32_SCB_FPCCR_MMRDY_SHIFT                5u
#define S32_SCB_FPCCR_MMRDY_WIDTH                1u
#define S32_SCB_FPCCR_MMRDY(x)                   (((uint32_t)(((uint32_t)(x))<<S32_SCB_FPCCR_MMRDY_SHIFT))&S32_SCB_FPCCR_MMRDY_MASK)
#define S32_SCB_FPCCR_BFRDY_MASK                 0x40u
#define S32_SCB_FPCCR_BFRDY_SHIFT                6u
#define S32_SCB_FPCCR_BFRDY_WIDTH                1u
#define S32_SCB_FPCCR_BFRDY(x)                   (((uint32_t)(((uint32_t)(x))<<S32_SCB_FPCCR_BFRDY_SHIFT))&S32_SCB_FPCCR_BFRDY_MASK)
#define S32_SCB_FPCCR_MONRDY_MASK                0x100u
#define S32_SCB_FPCCR_MONRDY_SHIFT               8u
#define S32_SCB_FPCCR_MONRDY_WIDTH               1u
#define S32_SCB_FPCCR_MONRDY(x)                  (((uint32_t)(((uint32_t)(x))<<S32_SCB_FPCCR_MONRDY_SHIFT))&S32_SCB_FPCCR_MONRDY_MASK)
#define S32_SCB_FPCCR_LSPEN_MASK                 0x40000000u
#define S32_SCB_FPCCR_LSPEN_SHIFT                30u
#define S32_SCB_FPCCR_LSPEN_WIDTH                1u
#define S32_SCB_FPCCR_LSPEN(x)                   (((uint32_t)(((uint32_t)(x))<<S32_SCB_FPCCR_LSPEN_SHIFT))&S32_SCB_FPCCR_LSPEN_MASK)
#define S32_SCB_FPCCR_ASPEN_MASK                 0x80000000u
#define S32_SCB_FPCCR_ASPEN_SHIFT                31u
#define S32_SCB_FPCCR_ASPEN_WIDTH                1u
#define S32_SCB_FPCCR_ASPEN(x)                   (((uint32_t)(((uint32_t)(x))<<S32_SCB_FPCCR_ASPEN_SHIFT))&S32_SCB_FPCCR_ASPEN_MASK)
/* FPCAR Bit Fields */
#define S32_SCB_FPCAR_ADDRESS_MASK               0xFFFFFFF8u
#define S32_SCB_FPCAR_ADDRESS_SHIFT              3u
#define S32_SCB_FPCAR_ADDRESS_WIDTH              29u
#define S32_SCB_FPCAR_ADDRESS(x)                 (((uint32_t)(((uint32_t)(x))<<S32_SCB_FPCAR_ADDRESS_SHIFT))&S32_SCB_FPCAR_ADDRESS_MASK)
/* FPDSCR Bit Fields */
#define S32_SCB_FPDSCR_RMode_MASK                0xC00000u
#define S32_SCB_FPDSCR_RMode_SHIFT               22u
#define S32_SCB_FPDSCR_RMode_WIDTH               2u
#define S32_SCB_FPDSCR_RMode(x)                  (((uint32_t)(((uint32_t)(x))<<S32_SCB_FPDSCR_RMode_SHIFT))&S32_SCB_FPDSCR_RMode_MASK)
#define S32_SCB_FPDSCR_FZ_MASK                   0x1000000u
#define S32_SCB_FPDSCR_FZ_SHIFT                  24u
#define S32_SCB_FPDSCR_FZ_WIDTH                  1u
#define S32_SCB_FPDSCR_FZ(x)                     (((uint32_t)(((uint32_t)(x))<<S32_SCB_FPDSCR_FZ_SHIFT))&S32_SCB_FPDSCR_FZ_MASK)
#define S32_SCB_FPDSCR_DN_MASK                   0x2000000u
#define S32_SCB_FPDSCR_DN_SHIFT                  25u
#define S32_SCB_FPDSCR_DN_WIDTH                  1u
#define S32_SCB_FPDSCR_DN(x)                     (((uint32_t)(((uint32_t)(x))<<S32_SCB_FPDSCR_DN_SHIFT))&S32_SCB_FPDSCR_DN_MASK)
#define S32_SCB_FPDSCR_AHP_MASK                  0x4000000u
#define S32_SCB_FPDSCR_AHP_SHIFT                 26u
#define S32_SCB_FPDSCR_AHP_WIDTH                 1u
#define S32_SCB_FPDSCR_AHP(x)                    (((uint32_t)(((uint32_t)(x))<<S32_SCB_FPDSCR_AHP_SHIFT))&S32_SCB_FPDSCR_AHP_MASK)

/*!
 * @}
 */ /* end of group S32_SCB_Register_Masks */


/*!
 * @}
 */ /* end of group S32_SCB_Peripheral_Access_Layer */

/*!
 * @brief Structure for the DMA hardware request
 *
 * Defines the structure for the DMA hardware request collections. The user can configure the
 * hardware request into DMAMUX to trigger the DMA transfer accordingly. The index
 * of the hardware request varies according  to the to SoC.
 */

typedef enum {
    EDMA_REQ_DISABLED = 0U,
    EDMA_REQ_LPUART0_RX = 2U,
    EDMA_REQ_LPUART0_TX = 3U,
    EDMA_REQ_LPUART1_RX = 4U,
    EDMA_REQ_LPUART1_TX = 5U,
    EDMA_REQ_FLEXIO_SHIFTER0 = 10U,
    EDMA_REQ_FLEXIO_SHIFTER1 = 11U,
    EDMA_REQ_FLEXIO_SHIFTER2 = 12U,
    EDMA_REQ_FLEXIO_SHIFTER3 = 13U,
    EDMA_REQ_LPSPI0_RX = 14U,
    EDMA_REQ_LPSPI0_TX = 15U,
    EDMA_REQ_LPSPI1_RX = 16U,
    EDMA_REQ_LPSPI1_TX = 17U,
    EDMA_REQ_FTM1_CHANNEL_0 = 20U,
    EDMA_REQ_FTM1_CHANNEL_1 = 21U,
    EDMA_REQ_FTM1_CHANNEL_2 = 22U,
    EDMA_REQ_FTM1_CHANNEL_3 = 23U,
    EDMA_REQ_FTM1_CHANNEL_4 = 24U,
    EDMA_REQ_FTM1_CHANNEL_5 = 25U,
    EDMA_REQ_FTM1_CHANNEL_6 = 26U,
    EDMA_REQ_FTM1_CHANNEL_7 = 27U,
    EDMA_REQ_FTM2_CHANNEL_0 = 28U,
    EDMA_REQ_FTM2_CHANNEL_1 = 29U,
    EDMA_REQ_FTM2_CHANNEL_2 = 30U,
    EDMA_REQ_FTM2_CHANNEL_3 = 31U,
    EDMA_REQ_FTM2_CHANNEL_4 = 32U,
    EDMA_REQ_FTM2_CHANNEL_5 = 33U,
    EDMA_REQ_FTM2_CHANNEL_6 = 34U,
    EDMA_REQ_FTM2_CHANNEL_7 = 35U,
    EDMA_REQ_FTM0_OR_CH0_CH7 = 36U,
    EDMA_REQ_FTM3_OR_CH0_CH7 = 37U,
    EDMA_REQ_ADC0 = 42U,
    EDMA_REQ_ADC1 = 43U,
    EDMA_REQ_LPI2C0_RX = 44U,
    EDMA_REQ_LPI2C0_TX = 45U,
    EDMA_REQ_PDB0 = 46U,
    EDMA_REQ_PDB1 = 47U,
    EDMA_REQ_CMP0 = 48U,
    EDMA_REQ_PORTA = 49U,
    EDMA_REQ_PORTB = 50U,
    EDMA_REQ_PORTC = 51U,
    EDMA_REQ_PORTD = 52U,
    EDMA_REQ_PORTE = 53U,
    EDMA_REQ_FLEXCAN0 = 54U,
    EDMA_REQ_FLEXCAN1 = 55U,
    EDMA_REQ_LPTMR0 = 59U,
    EDMA_REQ_DMAMUX_ALWAYS_ENABLED0 = 62U,
    EDMA_REQ_DMAMUX_ALWAYS_ENABLED1 = 63U
} dma_request_source_t;

/* LPIT module features */

/*! @brief Number of interrupt vector for channels of the LPIT module. */
#define FEATURE_LPIT_HAS_NUM_IRQS_CHANS                  (4U)
/*! @brief Clock names for LPIT. */
#define LPIT_CLOCK_NAMES    {LPIT0_CLK}

/* MSCM module features */

/* @brief Has interrupt router control registers (IRSPRCn). */
#define FEATURE_MSCM_HAS_INTERRUPT_ROUTER                (0)
/* @brief Has directed CPU interrupt routerregisters (IRCPxxx). */
#define FEATURE_MSCM_HAS_CPU_INTERRUPT_ROUTER            (0)


/* OSIF module features */

#define FEATURE_OSIF_USE_SYSTICK                         (1)
#define FEATURE_OSIF_USE_PIT                             (0)
#define FEATURE_OSIF_FREERTOS_ISR_CONTEXT_METHOD         (1) /* Cortex M device */

/* CAN module features */

/* @brief Frames available in Rx FIFO flag shift */
#define FEATURE_CAN_RXFIFO_FRAME_AVAILABLE  (5U)
/* @brief Rx FIFO warning flag shift */
#define FEATURE_CAN_RXFIFO_WARNING          (6U)
/* @brief Rx FIFO overflow flag shift */
#define FEATURE_CAN_RXFIFO_OVERFLOW         (7U)
/* @brief Has Flexible Data Rate for CAN0 */
#define FEATURE_CAN0_HAS_FD                 (1)
/* @brief Has Flexible Data Rate for CAN1 */
#define FEATURE_CAN1_HAS_FD                 (0)
/* @brief Maximum number of Message Buffers supported for payload size 8 for CAN0 */
#define FEATURE_CAN0_MAX_MB_NUM             (32U)
/* @brief Maximum number of Message Buffers supported for payload size 8 for CAN1 */
#define FEATURE_CAN1_MAX_MB_NUM             (16U)
/* @brief Has PE clock source select (bit field CAN_CTRL1[CLKSRC]). */
#define FEATURE_CAN_HAS_PE_CLKSRC_SELECT    (1)
/* @brief Has DMA enable (bit field MCR[DMA]). */
#define FEATURE_CAN_HAS_DMA_ENABLE          (1)
/* @brief Maximum number of Message Buffers supported for payload size 8 for any of the CAN instances */
#define FEATURE_CAN_MAX_MB_NUM              (32U)
/* @brief Maximum number of Message Buffers supported for payload size 8 for any of the CAN instances */
#define FEATURE_CAN_MAX_MB_NUM_ARRAY        { FEATURE_CAN0_MAX_MB_NUM, \
                                              FEATURE_CAN1_MAX_MB_NUM }
/* @brief Has Pretending Networking mode */
#define FEATURE_CAN_HAS_PRETENDED_NETWORKING    (1)
/* @brief Has Stuff Bit Count Enable Bit */
#define FEATURE_CAN_HAS_STFCNTEN_ENABLE         (0)
/* @brief Has ISO CAN FD Enable Bit */
#define FEATURE_CAN_HAS_ISOCANFDEN_ENABLE       (1)
/* @brief Has Message Buffer Data Size Region 1 */
#define FEATURE_CAN_HAS_MBDSR1                  (0)
/* @brief Has Message Buffer Data Size Region 2 */
#define FEATURE_CAN_HAS_MBDSR2                  (0)
/* @brief DMA hardware requests for all FlexCAN instances */
#define FEATURE_CAN_EDMA_REQUESTS              { EDMA_REQ_FLEXCAN0, \
                                                 EDMA_REQ_FLEXCAN1 }

/* @brief Maximum number of Message Buffers IRQs */
#define FEATURE_CAN_MB_IRQS_MAX_COUNT       (2U)
/* @brief Message Buffers IRQs */
#define FEATURE_CAN_MB_IRQS                 { CAN_ORed_0_15_MB_IRQS, \
                                              CAN_ORed_16_31_MB_IRQS }
/* @brief Has Wake Up Irq channels (CAN_Wake_Up_IRQS_CH_COUNT > 0u) */
#define FEATURE_CAN_HAS_WAKE_UP_IRQ         (1)
/* @brief Has Self Wake Up mode */
#define FEATURE_CAN_HAS_SELF_WAKE_UP        (0)
/* @brief Has Flexible Data Rate */
#define FEATURE_CAN_HAS_FD                  (1)
/* @brief Clock name for the PE oscillator clock source */
#define FEATURE_CAN_PE_OSC_CLK_NAME         SOSC_CLK
/* @bried FlexCAN has Detection And Correction of Memory Errors */
#define FEATURE_CAN_HAS_MEM_ERR_DET			(0)

/* LPSPI module features */
/* @brief Initial value for state structure */
#define FEATURE_LPSPI_STATE_STRUCTURES_NULL {NULL, NULL}
/* @brief Clock indexes for LPSPI clock */
#define FEATURE_LPSPI_CLOCKS_NAMES {LPSPI0_CLK, LPSPI1_CLK};

/* LPTMR module features */

/* @brief LPTMR pulse counter input options */
#define FEATURE_LPTMR_HAS_INPUT_ALT1_SELECTION  (1U)

/* TRGMUX module features */
/*!
 * @brief Enumeration for trigger source module of TRGMUX
 *
 * Describes all possible inputs (trigger sources) of the TRGMUX IP
 * This enumeration depends on the supported instances in device
 */
enum trgmux_trigger_source_e
{
    TRGMUX_TRIG_SOURCE_DISABLED             = 0U,
    TRGMUX_TRIG_SOURCE_VDD                  = 1U,
    TRGMUX_TRIG_SOURCE_TRGMUX_IN0           = 2U,
    TRGMUX_TRIG_SOURCE_TRGMUX_IN1           = 3U,
    TRGMUX_TRIG_SOURCE_TRGMUX_IN2           = 4U,
    TRGMUX_TRIG_SOURCE_TRGMUX_IN3           = 5U,
    TRGMUX_TRIG_SOURCE_TRGMUX_IN4           = 6U,
    TRGMUX_TRIG_SOURCE_TRGMUX_IN5           = 7U,
    TRGMUX_TRIG_SOURCE_TRGMUX_IN6           = 8U,
    TRGMUX_TRIG_SOURCE_TRGMUX_IN7           = 9U,
    TRGMUX_TRIG_SOURCE_TRGMUX_IN8           = 10U,
    TRGMUX_TRIG_SOURCE_TRGMUX_IN9           = 11U,
    TRGMUX_TRIG_SOURCE_TRGMUX_IN10          = 12U,
    TRGMUX_TRIG_SOURCE_TRGMUX_IN11          = 13U,
    TRGMUX_TRIG_SOURCE_CMP0_OUT             = 14U,
    TRGMUX_TRIG_SOURCE_LPIT_CH0             = 17U,
    TRGMUX_TRIG_SOURCE_LPIT_CH1             = 18U,
    TRGMUX_TRIG_SOURCE_LPIT_CH2             = 19U,
    TRGMUX_TRIG_SOURCE_LPIT_CH3             = 20U,
    TRGMUX_TRIG_SOURCE_LPTMR0               = 21U,
    TRGMUX_TRIG_SOURCE_FTM0_INIT_TRIG       = 22U,
    TRGMUX_TRIG_SOURCE_FTM0_EXT_TRIG        = 23U,
    TRGMUX_TRIG_SOURCE_FTM1_INIT_TRIG       = 24U,
    TRGMUX_TRIG_SOURCE_FTM1_EXT_TRIG        = 25U,
    TRGMUX_TRIG_SOURCE_FTM2_INIT_TRIG       = 26U,
    TRGMUX_TRIG_SOURCE_FTM2_EXT_TRIG        = 27U,
    TRGMUX_TRIG_SOURCE_FTM3_INIT_TRIG       = 28U,
    TRGMUX_TRIG_SOURCE_FTM3_EXT_TRIG        = 29U,
    TRGMUX_TRIG_SOURCE_ADC0_SC1A_COCO       = 30U,
    TRGMUX_TRIG_SOURCE_ADC0_SC1B_COCO       = 31U,
    TRGMUX_TRIG_SOURCE_ADC1_SC1A_COCO       = 32U,
    TRGMUX_TRIG_SOURCE_ADC1_SC1B_COCO       = 33U,
    TRGMUX_TRIG_SOURCE_PDB0_CH0_TRIG        = 34U,
    TRGMUX_TRIG_SOURCE_PDB0_PULSE_OUT       = 36U,
    TRGMUX_TRIG_SOURCE_PDB1_CH0_TRIG        = 37U,
    TRGMUX_TRIG_SOURCE_PDB1_PULSE_OUT       = 39U,
    TRGMUX_TRIG_SOURCE_RTC_ALARM            = 43U,
    TRGMUX_TRIG_SOURCE_RTC_SECOND           = 44U,
    TRGMUX_TRIG_SOURCE_FLEXIO_TRIG0         = 45U,
    TRGMUX_TRIG_SOURCE_FLEXIO_TRIG1         = 46U,
    TRGMUX_TRIG_SOURCE_FLEXIO_TRIG2         = 47U,
    TRGMUX_TRIG_SOURCE_FLEXIO_TRIG3         = 48U,
    TRGMUX_TRIG_SOURCE_LPUART0_RX_DATA      = 49U,
    TRGMUX_TRIG_SOURCE_LPUART0_TX_DATA      = 50U,
    TRGMUX_TRIG_SOURCE_LPUART0_RX_IDLE      = 51U,
    TRGMUX_TRIG_SOURCE_LPUART1_RX_DATA      = 52U,
    TRGMUX_TRIG_SOURCE_LPUART1_TX_DATA      = 53U,
    TRGMUX_TRIG_SOURCE_LPUART1_RX_IDLE      = 54U,
    TRGMUX_TRIG_SOURCE_LPI2C0_MASTER_TRIG   = 55U,
    TRGMUX_TRIG_SOURCE_LPI2C0_SLAVE_TRIG    = 56U,
    TRGMUX_TRIG_SOURCE_LPSPI0_FRAME         = 59U,
    TRGMUX_TRIG_SOURCE_LPSPI0_RX_DATA       = 60U,
    TRGMUX_TRIG_SOURCE_LPSPI1_FRAME         = 61U,
    TRGMUX_TRIG_SOURCE_LPSPI1_RX_DATA       = 62U,
    TRGMUX_TRIG_SOURCE_SIM_SW_TRIG          = 63U
};

/*!
 * @brief Enumeration for target module of TRGMUX
 *
 * Describes all possible outputs (target modules) of the TRGMUX IP
 * This enumeration depends on the supported instances in device
 */
enum trgmux_target_module_e
{
    TRGMUX_TARGET_MODULE_DMA_CH0            = 0U,
    TRGMUX_TARGET_MODULE_DMA_CH1            = 1U,
    TRGMUX_TARGET_MODULE_DMA_CH2            = 2U,
    TRGMUX_TARGET_MODULE_DMA_CH3            = 3U,
    TRGMUX_TARGET_MODULE_TRGMUX_OUT0        = 4U,
    TRGMUX_TARGET_MODULE_TRGMUX_OUT1        = 5U,
    TRGMUX_TARGET_MODULE_TRGMUX_OUT2        = 6U,
    TRGMUX_TARGET_MODULE_TRGMUX_OUT3        = 7U,
    TRGMUX_TARGET_MODULE_TRGMUX_OUT4        = 8U,
    TRGMUX_TARGET_MODULE_TRGMUX_OUT5        = 9U,
    TRGMUX_TARGET_MODULE_TRGMUX_OUT6        = 10U,
    TRGMUX_TARGET_MODULE_TRGMUX_OUT7        = 11U,
    TRGMUX_TARGET_MODULE_ADC0_ADHWT_TLA0    = 12U,
    TRGMUX_TARGET_MODULE_ADC0_ADHWT_TLA1    = 13U,
    TRGMUX_TARGET_MODULE_ADC0_ADHWT_TLA2    = 14U,
    TRGMUX_TARGET_MODULE_ADC0_ADHWT_TLA3    = 15U,
    TRGMUX_TARGET_MODULE_ADC1_ADHWT_TLA0    = 16U,
    TRGMUX_TARGET_MODULE_ADC1_ADHWT_TLA1    = 17U,
    TRGMUX_TARGET_MODULE_ADC1_ADHWT_TLA2    = 18U,
    TRGMUX_TARGET_MODULE_ADC1_ADHWT_TLA3    = 19U,
    TRGMUX_TARGET_MODULE_CMP0_SAMPLE        = 28U,
    TRGMUX_TARGET_MODULE_FTM0_HWTRIG0       = 40U,
    TRGMUX_TARGET_MODULE_FTM0_FAULT0        = 41U,
    TRGMUX_TARGET_MODULE_FTM0_FAULT1        = 42U,
    TRGMUX_TARGET_MODULE_FTM0_FAULT2        = 43U,
    TRGMUX_TARGET_MODULE_FTM1_HWTRIG0       = 44U,
    TRGMUX_TARGET_MODULE_FTM1_FAULT0        = 45U,
    TRGMUX_TARGET_MODULE_FTM1_FAULT1        = 46U,
    TRGMUX_TARGET_MODULE_FTM1_FAULT2        = 47U,
    TRGMUX_TARGET_MODULE_FTM2_HWTRIG0       = 48U,
    TRGMUX_TARGET_MODULE_FTM2_FAULT0        = 49U,
    TRGMUX_TARGET_MODULE_FTM2_FAULT1        = 50U,
    TRGMUX_TARGET_MODULE_FTM2_FAULT2        = 51U,
    TRGMUX_TARGET_MODULE_FTM3_HWTRIG0       = 52U,
    TRGMUX_TARGET_MODULE_FTM3_FAULT0        = 53U,
    TRGMUX_TARGET_MODULE_FTM3_FAULT1        = 54U,
    TRGMUX_TARGET_MODULE_FTM3_FAULT2        = 55U,
    TRGMUX_TARGET_MODULE_PDB0_TRG_IN        = 56U,
    TRGMUX_TARGET_MODULE_PDB1_TRG_IN        = 60U,
    TRGMUX_TARGET_MODULE_FLEXIO_TRG_TIM0    = 68U,
    TRGMUX_TARGET_MODULE_FLEXIO_TRG_TIM1    = 69U,
    TRGMUX_TARGET_MODULE_FLEXIO_TRG_TIM2    = 70U,
    TRGMUX_TARGET_MODULE_FLEXIO_TRG_TIM3    = 71U,
    TRGMUX_TARGET_MODULE_LPIT_TRG_CH0       = 72U,
    TRGMUX_TARGET_MODULE_LPIT_TRG_CH1       = 73U,
    TRGMUX_TARGET_MODULE_LPIT_TRG_CH2       = 74U,
    TRGMUX_TARGET_MODULE_LPIT_TRG_CH3       = 75U,
    TRGMUX_TARGET_MODULE_LPUART0_TRG        = 76U,
    TRGMUX_TARGET_MODULE_LPUART1_TRG        = 80U,
    TRGMUX_TARGET_MODULE_LPI2C0_TRG         = 84U,
    TRGMUX_TARGET_MODULE_LPSPI0_TRG         = 92U,
    TRGMUX_TARGET_MODULE_LPSPI1_TRG         = 96U,
    TRGMUX_TARGET_MODULE_LPTMR0_ALT0        = 100U
};

/* @brief Constant array storing the value of all TRGMUX output(target module) identifiers */
#define FEATURE_TRGMUX_TARGET_MODULE         \
{                                            \
    TRGMUX_TARGET_MODULE_DMA_CH0,            \
    TRGMUX_TARGET_MODULE_DMA_CH1,            \
    TRGMUX_TARGET_MODULE_DMA_CH2,            \
    TRGMUX_TARGET_MODULE_DMA_CH3,            \
    TRGMUX_TARGET_MODULE_TRGMUX_OUT0,        \
    TRGMUX_TARGET_MODULE_TRGMUX_OUT1,        \
    TRGMUX_TARGET_MODULE_TRGMUX_OUT2,        \
    TRGMUX_TARGET_MODULE_TRGMUX_OUT3,        \
    TRGMUX_TARGET_MODULE_TRGMUX_OUT4,        \
    TRGMUX_TARGET_MODULE_TRGMUX_OUT5,        \
    TRGMUX_TARGET_MODULE_TRGMUX_OUT6,        \
    TRGMUX_TARGET_MODULE_TRGMUX_OUT7,        \
    TRGMUX_TARGET_MODULE_ADC0_ADHWT_TLA0,    \
    TRGMUX_TARGET_MODULE_ADC0_ADHWT_TLA1,    \
    TRGMUX_TARGET_MODULE_ADC0_ADHWT_TLA2,    \
    TRGMUX_TARGET_MODULE_ADC0_ADHWT_TLA3,    \
    TRGMUX_TARGET_MODULE_ADC1_ADHWT_TLA0,    \
    TRGMUX_TARGET_MODULE_ADC1_ADHWT_TLA1,    \
    TRGMUX_TARGET_MODULE_ADC1_ADHWT_TLA2,    \
    TRGMUX_TARGET_MODULE_ADC1_ADHWT_TLA3,    \
    TRGMUX_TARGET_MODULE_CMP0_SAMPLE,        \
    TRGMUX_TARGET_MODULE_FTM0_HWTRIG0,       \
    TRGMUX_TARGET_MODULE_FTM0_FAULT0,        \
    TRGMUX_TARGET_MODULE_FTM0_FAULT1,        \
    TRGMUX_TARGET_MODULE_FTM0_FAULT2,        \
    TRGMUX_TARGET_MODULE_FTM1_HWTRIG0,       \
    TRGMUX_TARGET_MODULE_FTM1_FAULT0,        \
    TRGMUX_TARGET_MODULE_FTM1_FAULT1,        \
    TRGMUX_TARGET_MODULE_FTM1_FAULT2,        \
    TRGMUX_TARGET_MODULE_FTM2_HWTRIG0,       \
    TRGMUX_TARGET_MODULE_FTM2_FAULT0,        \
    TRGMUX_TARGET_MODULE_FTM2_FAULT1,        \
    TRGMUX_TARGET_MODULE_FTM2_FAULT2,        \
    TRGMUX_TARGET_MODULE_FTM3_HWTRIG0,       \
    TRGMUX_TARGET_MODULE_FTM3_FAULT0,        \
    TRGMUX_TARGET_MODULE_FTM3_FAULT1,        \
    TRGMUX_TARGET_MODULE_FTM3_FAULT2,        \
    TRGMUX_TARGET_MODULE_PDB0_TRG_IN,        \
    TRGMUX_TARGET_MODULE_PDB1_TRG_IN,        \
    TRGMUX_TARGET_MODULE_FLEXIO_TRG_TIM0,    \
    TRGMUX_TARGET_MODULE_FLEXIO_TRG_TIM1,    \
    TRGMUX_TARGET_MODULE_FLEXIO_TRG_TIM2,    \
    TRGMUX_TARGET_MODULE_FLEXIO_TRG_TIM3,    \
    TRGMUX_TARGET_MODULE_LPIT_TRG_CH0,       \
    TRGMUX_TARGET_MODULE_LPIT_TRG_CH1,       \
    TRGMUX_TARGET_MODULE_LPIT_TRG_CH2,       \
    TRGMUX_TARGET_MODULE_LPIT_TRG_CH3,       \
    TRGMUX_TARGET_MODULE_LPUART0_TRG,        \
    TRGMUX_TARGET_MODULE_LPUART1_TRG,        \
    TRGMUX_TARGET_MODULE_LPI2C0_TRG,         \
    TRGMUX_TARGET_MODULE_LPSPI0_TRG,         \
    TRGMUX_TARGET_MODULE_LPSPI1_TRG,         \
    TRGMUX_TARGET_MODULE_LPTMR0_ALT0         \
}

/* ISELED Pins */

#define ISELED_PIN_0     0    /*PTA10*/
#define ISELED_PIN_1     1    /*PTD0*/
#define ISELED_PIN_2     2    /*PTD9*/
#define ISELED_PIN_3     3    /*PTA11*/
#define ISELED_PIN_4     4    /*PTD1*/
#define ISELED_PIN_5     5    /*PTD8*/
#define ISELED_PIN_6     6    /*PTA0*/
#define ISELED_PIN_7     7    /*PTE15*/
#define ISELED_PIN_8     8    /*PTA1*/
#define ISELED_PIN_9     9    /*PTE16*/
#define ISELED_PIN_10    10    /*PTA2*/
#define ISELED_PIN_11    11    /*PTD2*/
#define ISELED_PIN_12    12    /*PTE10*/
#define ISELED_PIN_13    13    /*PTA3*/
#define ISELED_PIN_14    14    /*PTE11*/
#define ISELED_PIN_15    15    /*PTD3*/
#define ISELED_PIN_16    16    /*PTA8*/
#define ISELED_PIN_17    17    /*PTE3*/
#define ISELED_PIN_18    18    /*PTA9*/
#define ISELED_PIN_19    19    /*PTE3*/

#define ISELED_PIN_20    20    /*PTB2*/
#define ISELED_PIN_21    21    /*PTB1*/
#define ISELED_PIN_22    22    /*PTD15*/
#define ISELED_PIN_23    23    /*PTB4*/
#define ISELED_PIN_24    24    /*PTE0*/
#define ISELED_PIN_25    25    /*PTE2*/
#define ISELED_PIN_26    26    /*PTD0*/
#define ISELED_PIN_27    27    /*PTD2*/
#define ISELED_PIN_28    28    /*PTB14*/
#define ISELED_PIN_29    29    /*PTB16*/
#define ISELED_PIN_30    30    /*PTE15*/
#define ISELED_PIN_31    31    /*PTA8*/
#define ISELED_PIN_32    32    /*PTC15*/
#define ISELED_PIN_33    33    /*PTC1*/

#define ISELED_PIN_34    34    /*PTE1*/
#define ISELED_PIN_35    35    /*PTB3*/
#define ISELED_PIN_36    36    /*PTD16*/
#define ISELED_PIN_37    37    /*PTB15*/
#define ISELED_PIN_38    38    /*PTD1*/
#define ISELED_PIN_39    39    /*PTC0*/

#define MAX_NR_OF_STRIPS 13U


/* PDB module features */

/* @brief PDB has instance back to back mode between PDB0 CH0 and PDB1 CH0 pre-triggers */
#define FEATURE_PDB_HAS_INSTANCE_BACKTOBACK  (1)

/* @brief PDB has inter-channel back to back mode between PDBx CH0 and PDBx CH1 pre-triggers */
#define FEATURE_PDB_HAS_INTERCHANNEL_BACKTOBACK (0)


#endif /* S32K142_FEATURES_H */

/*******************************************************************************
 * EOF
 ******************************************************************************/
