robert-lippmann/ft-RPI-sa/Software/include/S32_system.h

/*
 * S32_system.h
 *
 *  Created on: 17.10.2024
 *      Author: nxa19914
 */

#ifndef S32_SYSTEM_H_
#define S32_SYSTEM_H_

#include <stdint.h>

#ifndef __IO
#ifdef __cplusplus
  #define   __I     volatile             /*!< Defines 'read only' permissions                 */
#else
  #define   __I     volatile const       /*!< Defines 'read only' permissions                 */
#endif
#define     __O     volatile             /*!< Defines 'write only' permissions                */
#define     __IO    volatile             /*!< Defines 'read / write' permissions              */
#endif

/* ----------------------------------------------------------------------------
   -- S32_NVIC Peripheral Access Layer
   ---------------------------------------------------------------------------- */

/*!
 * @addtogroup S32_NVIC_Peripheral_Access_Layer S32_NVIC Peripheral Access Layer
 * @{
 */


/** S32_NVIC - Size of Registers Arrays */
#define S32_NVIC_ISER_COUNT                      8u
#define S32_NVIC_ICER_COUNT                      8u
#define S32_NVIC_ISPR_COUNT                      8u
#define S32_NVIC_ICPR_COUNT                      8u
#define S32_NVIC_IABR_COUNT                      8u
#define S32_NVIC_IP_COUNT                        240u

/** S32_NVIC - Register Layout Typedef */
typedef struct {
  __IO uint32_t ISER[S32_NVIC_ISER_COUNT];         /**< Interrupt Set Enable Register n, array offset: 0x0, array step: 0x4 */
       uint8_t RESERVED_0[96];
  __IO uint32_t ICER[S32_NVIC_ICER_COUNT];         /**< Interrupt Clear Enable Register n, array offset: 0x80, array step: 0x4 */
       uint8_t RESERVED_1[96];
  __IO uint32_t ISPR[S32_NVIC_ISPR_COUNT];         /**< Interrupt Set Pending Register n, array offset: 0x100, array step: 0x4 */
       uint8_t RESERVED_2[96];
  __IO uint32_t ICPR[S32_NVIC_ICPR_COUNT];         /**< Interrupt Clear Pending Register n, array offset: 0x180, array step: 0x4 */
       uint8_t RESERVED_3[96];
  __IO uint32_t IABR[S32_NVIC_IABR_COUNT];         /**< Interrupt Active bit Register n, array offset: 0x200, array step: 0x4 */
       uint8_t RESERVED_4[224];
  __IO uint8_t IP[S32_NVIC_IP_COUNT];              /**< Interrupt Priority Register n, array offset: 0x300, array step: 0x1 */
       uint8_t RESERVED_5[2576];
  __O  uint32_t STIR;                              /**< Software Trigger Interrupt Register, offset: 0xE00 */
} S32_NVIC_Type, *S32_NVIC_MemMapPtr;

 /** Number of instances of the S32_NVIC module. */
#define S32_NVIC_INSTANCE_COUNT                  (1u)


/* S32_NVIC - Peripheral instance base addresses */
/** Peripheral S32_NVIC base address */
#define S32_NVIC_BASE                            (0xE000E100u)
/** Peripheral S32_NVIC base pointer */
#define S32_NVIC                                 ((S32_NVIC_Type *)S32_NVIC_BASE)
/** Array initializer of S32_NVIC peripheral base addresses */
#define S32_NVIC_BASE_ADDRS                      { S32_NVIC_BASE }
/** Array initializer of S32_NVIC peripheral base pointers */
#define S32_NVIC_BASE_PTRS                       { S32_NVIC }
 /** Number of interrupt vector arrays for the S32_NVIC module. */
#define S32_NVIC_IRQS_ARR_COUNT                  (1u)
 /** Number of interrupt channels for the S32_NVIC module. */
#define S32_NVIC_IRQS_CH_COUNT                   (1u)
/** Interrupt vectors for the S32_NVIC peripheral type */
#define S32_NVIC_IRQS                            { SWI_IRQn }

/* ----------------------------------------------------------------------------
   -- S32_NVIC Register Masks
   ---------------------------------------------------------------------------- */

/*!
 * @addtogroup S32_NVIC_Register_Masks S32_NVIC Register Masks
 * @{
 */

/* ISER Bit Fields */
#define S32_NVIC_ISER_SETENA_MASK                0xFFFFFFFFu
#define S32_NVIC_ISER_SETENA_SHIFT               0u
#define S32_NVIC_ISER_SETENA_WIDTH               32u
#define S32_NVIC_ISER_SETENA(x)                  (((uint32_t)(((uint32_t)(x))<<S32_NVIC_ISER_SETENA_SHIFT))&S32_NVIC_ISER_SETENA_MASK)
/* ICER Bit Fields */
#define S32_NVIC_ICER_CLRENA_MASK                0xFFFFFFFFu
#define S32_NVIC_ICER_CLRENA_SHIFT               0u
#define S32_NVIC_ICER_CLRENA_WIDTH               32u
#define S32_NVIC_ICER_CLRENA(x)                  (((uint32_t)(((uint32_t)(x))<<S32_NVIC_ICER_CLRENA_SHIFT))&S32_NVIC_ICER_CLRENA_MASK)
/* ISPR Bit Fields */
#define S32_NVIC_ISPR_SETPEND_MASK               0xFFFFFFFFu
#define S32_NVIC_ISPR_SETPEND_SHIFT              0u
#define S32_NVIC_ISPR_SETPEND_WIDTH              32u
#define S32_NVIC_ISPR_SETPEND(x)                 (((uint32_t)(((uint32_t)(x))<<S32_NVIC_ISPR_SETPEND_SHIFT))&S32_NVIC_ISPR_SETPEND_MASK)
/* ICPR Bit Fields */
#define S32_NVIC_ICPR_CLRPEND_MASK               0xFFFFFFFFu
#define S32_NVIC_ICPR_CLRPEND_SHIFT              0u
#define S32_NVIC_ICPR_CLRPEND_WIDTH              32u
#define S32_NVIC_ICPR_CLRPEND(x)                 (((uint32_t)(((uint32_t)(x))<<S32_NVIC_ICPR_CLRPEND_SHIFT))&S32_NVIC_ICPR_CLRPEND_MASK)
/* IABR Bit Fields */
#define S32_NVIC_IABR_ACTIVE_MASK                0xFFFFFFFFu
#define S32_NVIC_IABR_ACTIVE_SHIFT               0u
#define S32_NVIC_IABR_ACTIVE_WIDTH               32u
#define S32_NVIC_IABR_ACTIVE(x)                  (((uint32_t)(((uint32_t)(x))<<S32_NVIC_IABR_ACTIVE_SHIFT))&S32_NVIC_IABR_ACTIVE_MASK)
/* IP Bit Fields */
#define S32_NVIC_IP_PRI0_MASK                    0xFFu
#define S32_NVIC_IP_PRI0_SHIFT                   0u
#define S32_NVIC_IP_PRI0_WIDTH                   8u
#define S32_NVIC_IP_PRI0(x)                      (((uint8_t)(((uint8_t)(x))<<S32_NVIC_IP_PRI0_SHIFT))&S32_NVIC_IP_PRI0_MASK)
#define S32_NVIC_IP_PRI1_MASK                    0xFFu
#define S32_NVIC_IP_PRI1_SHIFT                   0u
#define S32_NVIC_IP_PRI1_WIDTH                   8u
#define S32_NVIC_IP_PRI1(x)                      (((uint8_t)(((uint8_t)(x))<<S32_NVIC_IP_PRI1_SHIFT))&S32_NVIC_IP_PRI1_MASK)
#define S32_NVIC_IP_PRI2_MASK                    0xFFu
#define S32_NVIC_IP_PRI2_SHIFT                   0u
#define S32_NVIC_IP_PRI2_WIDTH                   8u
#define S32_NVIC_IP_PRI2(x)                      (((uint8_t)(((uint8_t)(x))<<S32_NVIC_IP_PRI2_SHIFT))&S32_NVIC_IP_PRI2_MASK)
#define S32_NVIC_IP_PRI3_MASK                    0xFFu
#define S32_NVIC_IP_PRI3_SHIFT                   0u
#define S32_NVIC_IP_PRI3_WIDTH                   8u
#define S32_NVIC_IP_PRI3(x)                      (((uint8_t)(((uint8_t)(x))<<S32_NVIC_IP_PRI3_SHIFT))&S32_NVIC_IP_PRI3_MASK)
#define S32_NVIC_IP_PRI4_MASK                    0xFFu
#define S32_NVIC_IP_PRI4_SHIFT                   0u
#define S32_NVIC_IP_PRI4_WIDTH                   8u
#define S32_NVIC_IP_PRI4(x)                      (((uint8_t)(((uint8_t)(x))<<S32_NVIC_IP_PRI4_SHIFT))&S32_NVIC_IP_PRI4_MASK)
#define S32_NVIC_IP_PRI5_MASK                    0xFFu
#define S32_NVIC_IP_PRI5_SHIFT                   0u
#define S32_NVIC_IP_PRI5_WIDTH                   8u
#define S32_NVIC_IP_PRI5(x)                      (((uint8_t)(((uint8_t)(x))<<S32_NVIC_IP_PRI5_SHIFT))&S32_NVIC_IP_PRI5_MASK)
#define S32_NVIC_IP_PRI6_MASK                    0xFFu
#define S32_NVIC_IP_PRI6_SHIFT                   0u
#define S32_NVIC_IP_PRI6_WIDTH                   8u
#define S32_NVIC_IP_PRI6(x)                      (((uint8_t)(((uint8_t)(x))<<S32_NVIC_IP_PRI6_SHIFT))&S32_NVIC_IP_PRI6_MASK)
#define S32_NVIC_IP_PRI7_MASK                    0xFFu
#define S32_NVIC_IP_PRI7_SHIFT                   0u
#define S32_NVIC_IP_PRI7_WIDTH                   8u
#define S32_NVIC_IP_PRI7(x)                      (((uint8_t)(((uint8_t)(x))<<S32_NVIC_IP_PRI7_SHIFT))&S32_NVIC_IP_PRI7_MASK)
#define S32_NVIC_IP_PRI8_MASK                    0xFFu
#define S32_NVIC_IP_PRI8_SHIFT                   0u
#define S32_NVIC_IP_PRI8_WIDTH                   8u
#define S32_NVIC_IP_PRI8(x)                      (((uint8_t)(((uint8_t)(x))<<S32_NVIC_IP_PRI8_SHIFT))&S32_NVIC_IP_PRI8_MASK)
#define S32_NVIC_IP_PRI9_MASK                    0xFFu
#define S32_NVIC_IP_PRI9_SHIFT                   0u
#define S32_NVIC_IP_PRI9_WIDTH                   8u
#define S32_NVIC_IP_PRI9(x)                      (((uint8_t)(((uint8_t)(x))<<S32_NVIC_IP_PRI9_SHIFT))&S32_NVIC_IP_PRI9_MASK)
#define S32_NVIC_IP_PRI10_MASK                   0xFFu
#define S32_NVIC_IP_PRI10_SHIFT                  0u
#define S32_NVIC_IP_PRI10_WIDTH                  8u
#define S32_NVIC_IP_PRI10(x)                     (((uint8_t)(((uint8_t)(x))<<S32_NVIC_IP_PRI10_SHIFT))&S32_NVIC_IP_PRI10_MASK)
#define S32_NVIC_IP_PRI11_MASK                   0xFFu
#define S32_NVIC_IP_PRI11_SHIFT                  0u
#define S32_NVIC_IP_PRI11_WIDTH                  8u
#define S32_NVIC_IP_PRI11(x)                     (((uint8_t)(((uint8_t)(x))<<S32_NVIC_IP_PRI11_SHIFT))&S32_NVIC_IP_PRI11_MASK)
#define S32_NVIC_IP_PRI12_MASK                   0xFFu
#define S32_NVIC_IP_PRI12_SHIFT                  0u
#define S32_NVIC_IP_PRI12_WIDTH                  8u
#define S32_NVIC_IP_PRI12(x)                     (((uint8_t)(((uint8_t)(x))<<S32_NVIC_IP_PRI12_SHIFT))&S32_NVIC_IP_PRI12_MASK)
#define S32_NVIC_IP_PRI13_MASK                   0xFFu
#define S32_NVIC_IP_PRI13_SHIFT                  0u
#define S32_NVIC_IP_PRI13_WIDTH                  8u
#define S32_NVIC_IP_PRI13(x)                     (((uint8_t)(((uint8_t)(x))<<S32_NVIC_IP_PRI13_SHIFT))&S32_NVIC_IP_PRI13_MASK)
#define S32_NVIC_IP_PRI14_MASK                   0xFFu
#define S32_NVIC_IP_PRI14_SHIFT                  0u
#define S32_NVIC_IP_PRI14_WIDTH                  8u
#define S32_NVIC_IP_PRI14(x)                     (((uint8_t)(((uint8_t)(x))<<S32_NVIC_IP_PRI14_SHIFT))&S32_NVIC_IP_PRI14_MASK)
#define S32_NVIC_IP_PRI15_MASK                   0xFFu
#define S32_NVIC_IP_PRI15_SHIFT                  0u
#define S32_NVIC_IP_PRI15_WIDTH                  8u
#define S32_NVIC_IP_PRI15(x)                     (((uint8_t)(((uint8_t)(x))<<S32_NVIC_IP_PRI15_SHIFT))&S32_NVIC_IP_PRI15_MASK)
#define S32_NVIC_IP_PRI16_MASK                   0xFFu
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
#define S32_NVIC_IP_PRI233(x)                    (((uint8_t)(((uint8_t)(x))<<S32_NVIC_IP_PRI233_SHIFT))&S32_NVIC_IP_PRI233_MASK)
#define S32_NVIC_IP_PRI234_MASK                  0xFFu
#define S32_NVIC_IP_PRI234_SHIFT                 0u
#define S32_NVIC_IP_PRI234_WIDTH                 8u
#define S32_NVIC_IP_PRI234(x)                    (((uint8_t)(((uint8_t)(x))<<S32_NVIC_IP_PRI234_SHIFT))&S32_NVIC_IP_PRI234_MASK)
#define S32_NVIC_IP_PRI235_MASK                  0xFFu
#define S32_NVIC_IP_PRI235_SHIFT                 0u
#define S32_NVIC_IP_PRI235_WIDTH                 8u
#define S32_NVIC_IP_PRI235(x)                    (((uint8_t)(((uint8_t)(x))<<S32_NVIC_IP_PRI235_SHIFT))&S32_NVIC_IP_PRI235_MASK)
#define S32_NVIC_IP_PRI236_MASK                  0xFFu
#define S32_NVIC_IP_PRI236_SHIFT                 0u
#define S32_NVIC_IP_PRI236_WIDTH                 8u
#define S32_NVIC_IP_PRI236(x)                    (((uint8_t)(((uint8_t)(x))<<S32_NVIC_IP_PRI236_SHIFT))&S32_NVIC_IP_PRI236_MASK)
#define S32_NVIC_IP_PRI237_MASK                  0xFFu
#define S32_NVIC_IP_PRI237_SHIFT                 0u
#define S32_NVIC_IP_PRI237_WIDTH                 8u
#define S32_NVIC_IP_PRI237(x)                    (((uint8_t)(((uint8_t)(x))<<S32_NVIC_IP_PRI237_SHIFT))&S32_NVIC_IP_PRI237_MASK)
#define S32_NVIC_IP_PRI238_MASK                  0xFFu
#define S32_NVIC_IP_PRI238_SHIFT                 0u
#define S32_NVIC_IP_PRI238_WIDTH                 8u
#define S32_NVIC_IP_PRI238(x)                    (((uint8_t)(((uint8_t)(x))<<S32_NVIC_IP_PRI238_SHIFT))&S32_NVIC_IP_PRI238_MASK)
#define S32_NVIC_IP_PRI239_MASK                  0xFFu
#define S32_NVIC_IP_PRI239_SHIFT                 0u
#define S32_NVIC_IP_PRI239_WIDTH                 8u
#define S32_NVIC_IP_PRI239(x)                    (((uint8_t)(((uint8_t)(x))<<S32_NVIC_IP_PRI239_SHIFT))&S32_NVIC_IP_PRI239_MASK)
/* STIR Bit Fields */
#define S32_NVIC_STIR_INTID_MASK                 0x1FFu
#define S32_NVIC_STIR_INTID_SHIFT                0u
#define S32_NVIC_STIR_INTID_WIDTH                9u
#define S32_NVIC_STIR_INTID(x)                   (((uint32_t)(((uint32_t)(x))<<S32_NVIC_STIR_INTID_SHIFT))&S32_NVIC_STIR_INTID_MASK)

/*!
 * @}
 */ /* end of group S32_NVIC_Register_Masks */


/*!
 * @}
 */ /* end of group S32_NVIC_Peripheral_Access_Layer */

/* ----------------------------------------------------------------------------
   -- S32_SysTick Peripheral Access Layer
   ---------------------------------------------------------------------------- */

/*!
 * @addtogroup S32_SysTick_Peripheral_Access_Layer S32_SysTick Peripheral Access Layer
 * @{
 */


/** S32_SysTick - Size of Registers Arrays */

/** S32_SysTick - Register Layout Typedef */
typedef struct {
  __IO uint32_t CSR;                               /**< SysTick Control and Status Register, offset: 0x0 */
  __IO uint32_t RVR;                               /**< SysTick Reload Value Register, offset: 0x4 */
  __IO uint32_t CVR;                               /**< SysTick Current Value Register, offset: 0x8 */
  __I  uint32_t CALIB;                             /**< SysTick Calibration Value Register, offset: 0xC */
} S32_SysTick_Type, *S32_SysTick_MemMapPtr;

 /** Number of instances of the S32_SysTick module. */
#define S32_SysTick_INSTANCE_COUNT               (1u)


/* S32_SysTick - Peripheral instance base addresses */
/** Peripheral S32_SysTick base address */
#define S32_SysTick_BASE                         (0xE000E010u)
/** Peripheral S32_SysTick base pointer */
#define S32_SysTick                              ((S32_SysTick_Type *)S32_SysTick_BASE)
/** Array initializer of S32_SysTick peripheral base addresses */
#define S32_SysTick_BASE_ADDRS                   { S32_SysTick_BASE }
/** Array initializer of S32_SysTick peripheral base pointers */
#define S32_SysTick_BASE_PTRS                    { S32_SysTick }
 /** Number of interrupt vector arrays for the S32_SysTick module. */
#define S32_SysTick_IRQS_ARR_COUNT               (1u)
 /** Number of interrupt channels for the S32_SysTick module. */
#define S32_SysTick_IRQS_CH_COUNT                (1u)
/** Interrupt vectors for the S32_SysTick peripheral type */
#define S32_SysTick_IRQS                         { SysTick_IRQn }

/* ----------------------------------------------------------------------------
   -- S32_SysTick Register Masks
   ---------------------------------------------------------------------------- */

/*!
 * @addtogroup S32_SysTick_Register_Masks S32_SysTick Register Masks
 * @{
 */

/* CSR Bit Fields */
#define S32_SysTick_CSR_ENABLE_MASK              0x1u
#define S32_SysTick_CSR_ENABLE_SHIFT             0u
#define S32_SysTick_CSR_ENABLE_WIDTH             1u
#define S32_SysTick_CSR_ENABLE(x)                (((uint32_t)(((uint32_t)(x))<<S32_SysTick_CSR_ENABLE_SHIFT))&S32_SysTick_CSR_ENABLE_MASK)
#define S32_SysTick_CSR_TICKINT_MASK             0x2u
#define S32_SysTick_CSR_TICKINT_SHIFT            1u
#define S32_SysTick_CSR_TICKINT_WIDTH            1u
#define S32_SysTick_CSR_TICKINT(x)               (((uint32_t)(((uint32_t)(x))<<S32_SysTick_CSR_TICKINT_SHIFT))&S32_SysTick_CSR_TICKINT_MASK)
#define S32_SysTick_CSR_CLKSOURCE_MASK           0x4u
#define S32_SysTick_CSR_CLKSOURCE_SHIFT          2u
#define S32_SysTick_CSR_CLKSOURCE_WIDTH          1u
#define S32_SysTick_CSR_CLKSOURCE(x)             (((uint32_t)(((uint32_t)(x))<<S32_SysTick_CSR_CLKSOURCE_SHIFT))&S32_SysTick_CSR_CLKSOURCE_MASK)
#define S32_SysTick_CSR_COUNTFLAG_MASK           0x10000u
#define S32_SysTick_CSR_COUNTFLAG_SHIFT          16u
#define S32_SysTick_CSR_COUNTFLAG_WIDTH          1u
#define S32_SysTick_CSR_COUNTFLAG(x)             (((uint32_t)(((uint32_t)(x))<<S32_SysTick_CSR_COUNTFLAG_SHIFT))&S32_SysTick_CSR_COUNTFLAG_MASK)
/* RVR Bit Fields */
#define S32_SysTick_RVR_RELOAD_MASK              0xFFFFFFu
#define S32_SysTick_RVR_RELOAD_SHIFT             0u
#define S32_SysTick_RVR_RELOAD_WIDTH             24u
#define S32_SysTick_RVR_RELOAD(x)                (((uint32_t)(((uint32_t)(x))<<S32_SysTick_RVR_RELOAD_SHIFT))&S32_SysTick_RVR_RELOAD_MASK)
/* CVR Bit Fields */
#define S32_SysTick_CVR_CURRENT_MASK             0xFFFFFFu
#define S32_SysTick_CVR_CURRENT_SHIFT            0u
#define S32_SysTick_CVR_CURRENT_WIDTH            24u
#define S32_SysTick_CVR_CURRENT(x)               (((uint32_t)(((uint32_t)(x))<<S32_SysTick_CVR_CURRENT_SHIFT))&S32_SysTick_CVR_CURRENT_MASK)
/* CALIB Bit Fields */
#define S32_SysTick_CALIB_TENMS_MASK             0xFFFFFFu
#define S32_SysTick_CALIB_TENMS_SHIFT            0u
#define S32_SysTick_CALIB_TENMS_WIDTH            24u
#define S32_SysTick_CALIB_TENMS(x)               (((uint32_t)(((uint32_t)(x))<<S32_SysTick_CALIB_TENMS_SHIFT))&S32_SysTick_CALIB_TENMS_MASK)
#define S32_SysTick_CALIB_SKEW_MASK              0x40000000u
#define S32_SysTick_CALIB_SKEW_SHIFT             30u
#define S32_SysTick_CALIB_SKEW_WIDTH             1u
#define S32_SysTick_CALIB_SKEW(x)                (((uint32_t)(((uint32_t)(x))<<S32_SysTick_CALIB_SKEW_SHIFT))&S32_SysTick_CALIB_SKEW_MASK)
#define S32_SysTick_CALIB_NOREF_MASK             0x80000000u
#define S32_SysTick_CALIB_NOREF_SHIFT            31u
#define S32_SysTick_CALIB_NOREF_WIDTH            1u
#define S32_SysTick_CALIB_NOREF(x)               (((uint32_t)(((uint32_t)(x))<<S32_SysTick_CALIB_NOREF_SHIFT))&S32_SysTick_CALIB_NOREF_MASK)

/*!
 * @}
 */ /* end of group S32_SysTick_Register_Masks */


/*!
 * @}
 */ /* end of group S32_SysTick_Peripheral_Access_Layer */



#endif /* S32_SYSTEM_H_ */
